chrisspen/saunterbot/circuits/external voltage reference/Vref.png

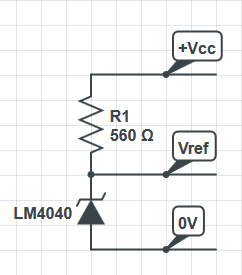
circuits/external voltage reference/Vref.png
