chrisspen/saunterbot/docs/img/bot/IMG_20180331_162108.jpg

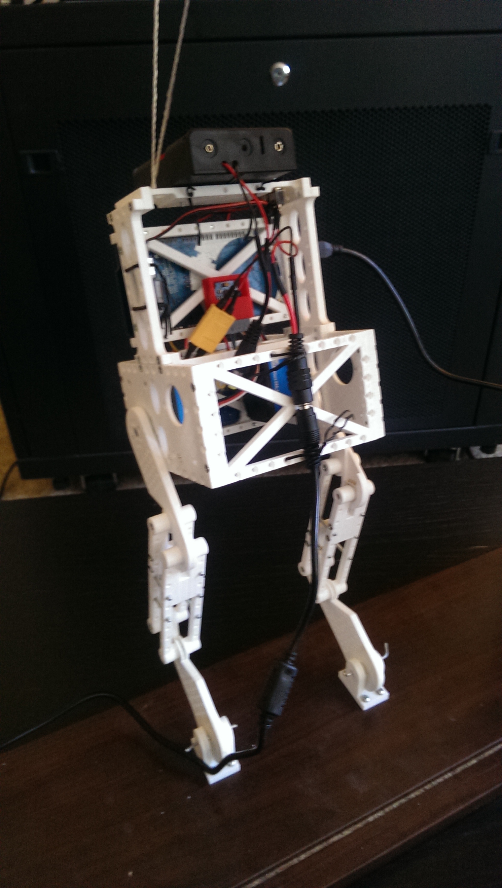
docs/img/bot/IMG_20180331_162108.jpg
