chrisspen/saunterbot/docs/img/bot/IMG_20180331_162210.jpg

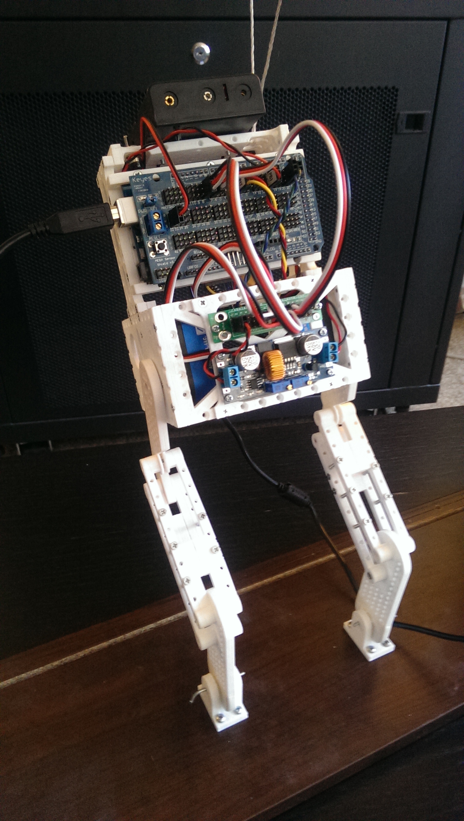
docs/img/bot/IMG_20180331_162210.jpg
