chrisspen/saunterbot/docs/img/bot/IMG_20180411_193514.jpg

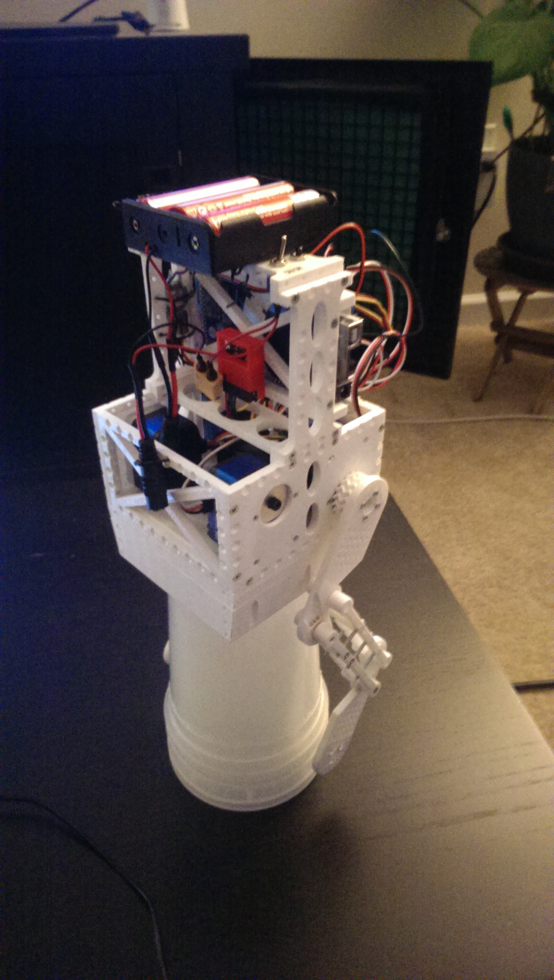
docs/img/bot/IMG_20180411_193514.jpg
