chrisspen/saunterbot/docs/img/bot/IMG_20180411_193522.jpg

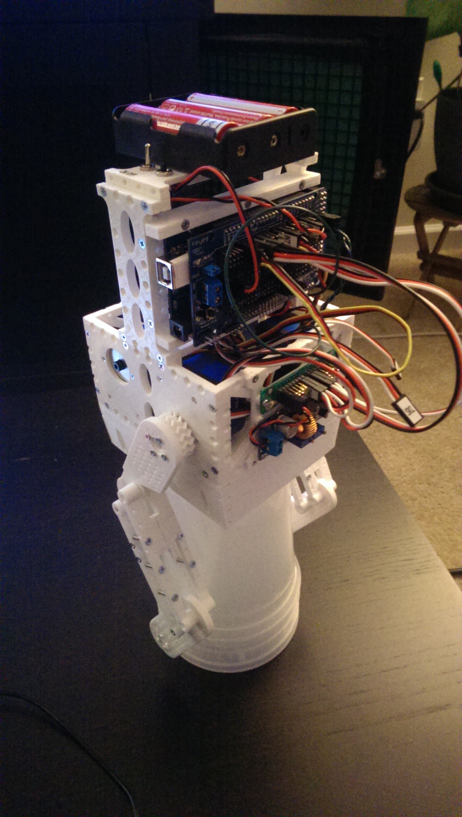
docs/img/bot/IMG_20180411_193522.jpg
