chrisspen/saunterbot/docs/img/bot/IMG_20180411_193531.jpg

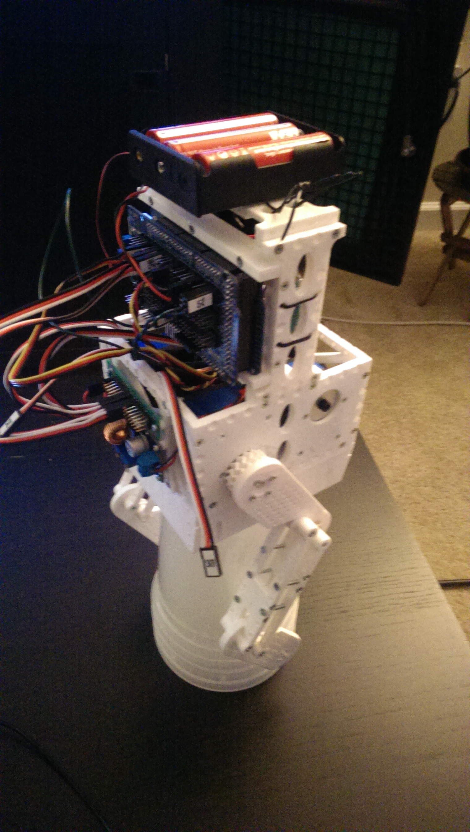
docs/img/bot/IMG_20180411_193531.jpg
