chrisspen/saunterbot/docs/img/bot/IMG_20180411_193601.jpg

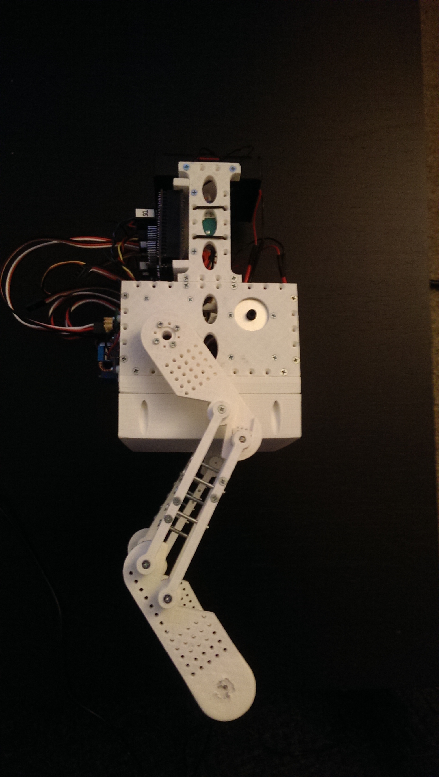
docs/img/bot/IMG_20180411_193601.jpg
