chrisspen/saunterbot/docs/img/bot/IMG_20180411_193617.jpg

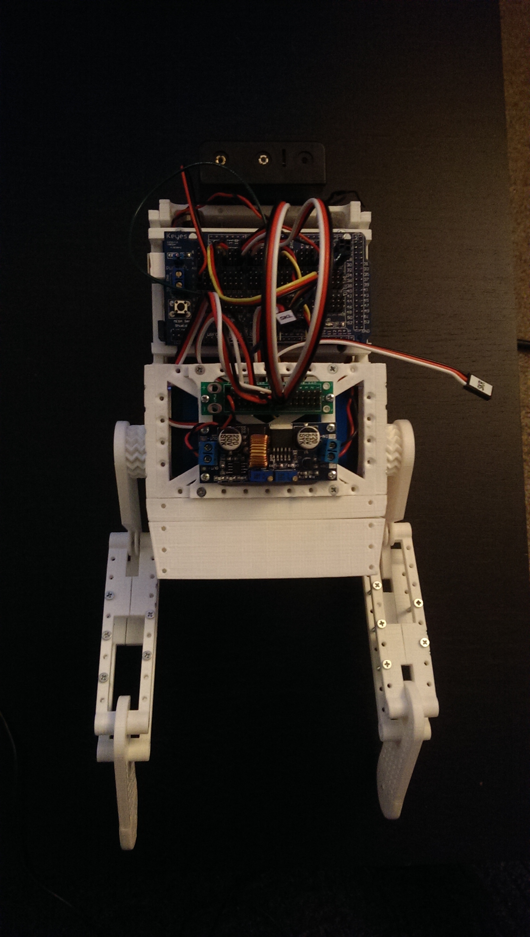
docs/img/bot/IMG_20180411_193617.jpg
