chrisspen/saunterbot/docs/img/bot/layout-cropped.png

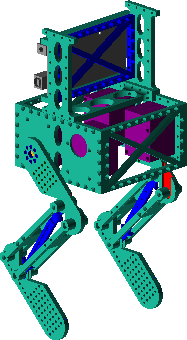
docs/img/bot/layout-cropped.png
