chrisspen/saunterbot/docs/img/bot/layout.png

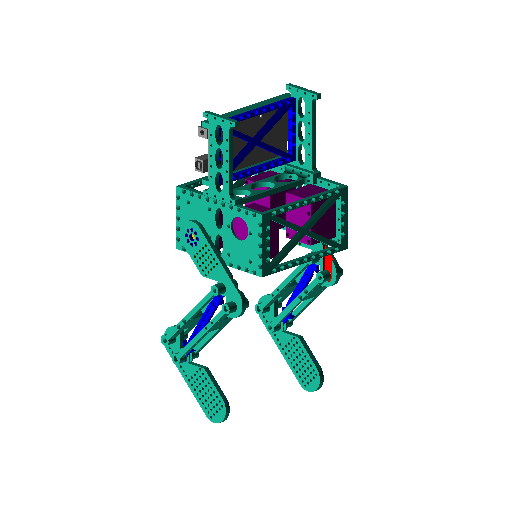
docs/img/bot/layout.png
