chrisspen/saunterbot/docs/img/dynamics-1-20180330.png

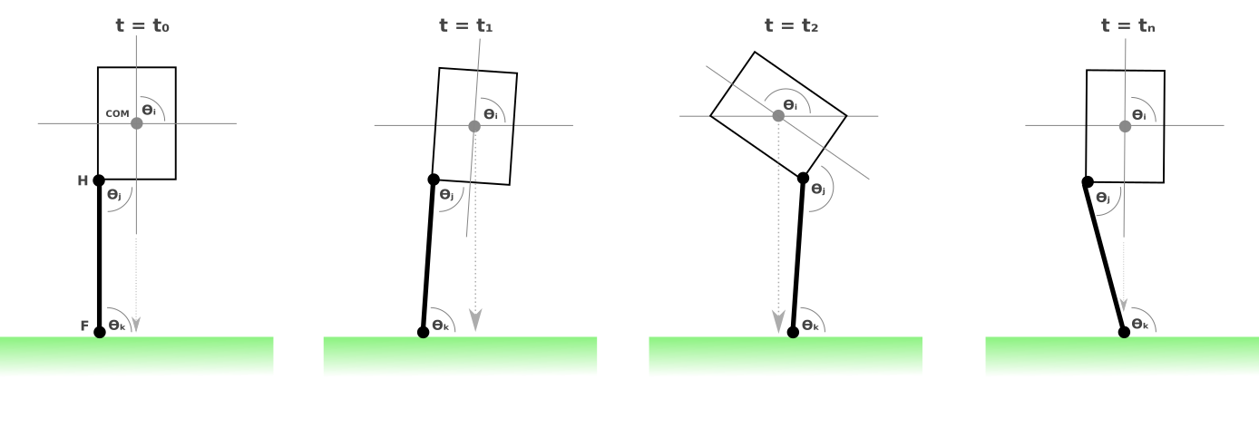
docs/img/dynamics-1-20180330.png
