chrisspen/saunterbot/docs/img/dynamics-1-20180331.png

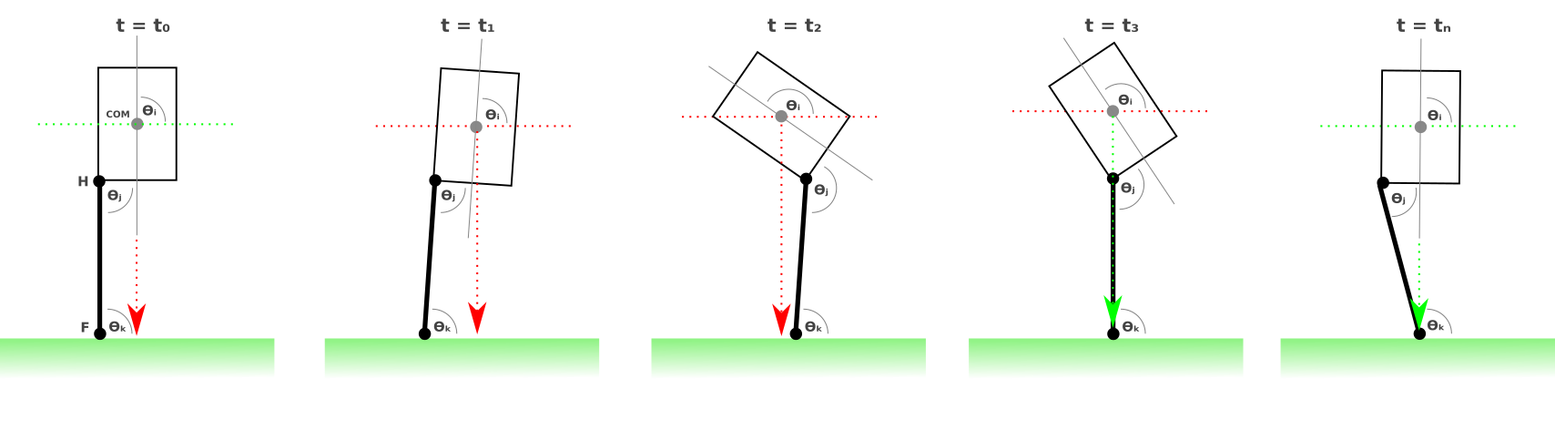
docs/img/dynamics-1-20180331.png
