chrisspen/saunterbot/docs/research/inverted pendulum/An-example-of-cart-table-model9.ppm.png

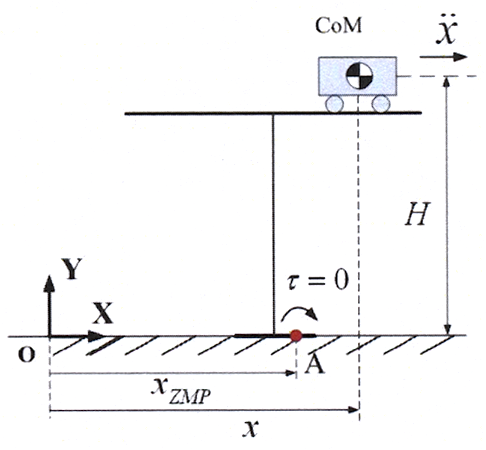
docs/research/inverted pendulum/An-example-of-cart-table-model9.ppm.png
