chrisspen/saunterbot/docs/research/legs/fncom-08-00027-g002.jpg

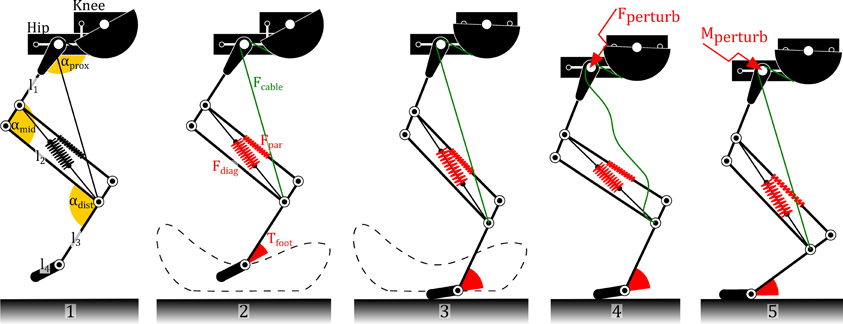
docs/research/legs/fncom-08-00027-g002.jpg
