chrisspen/saunterbot/models/electronics/hs-311-hitec-standard-servo/Renderings/aa.PNG

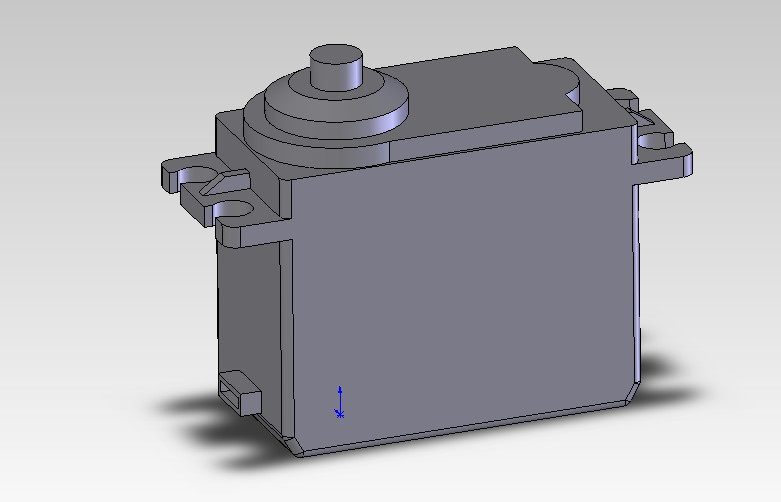
models/electronics/hs-311-hitec-standard-servo/Renderings/aa.PNG
