chrisspen/saunterbot/docs/parts/Arduino - Mega/README

Arduino Mega
============

https://store.arduino.cc/arduino-mega-2560-rev3

https://www.arduino.cc/en/Hacking/PinMapping2560
