chrisspen/saunterbot/docs/parts/Arduino Mega Sensor Shield v2.0/README

Sensor Shield for Arduino MEGA V2

http://yourduino.com/sunshop//index.php?l=product_detail&p=195
https://arduino-info.wikispaces.com/SensorShield
