chrisspen/saunterbot/docs/parts/Rotary Position Sensor - Model 3382/README

Rotary Position Sensor - Model 3382
===================================

https://www.digikey.com/products/en?keywords=3382G-1-104GCT-ND
