chrisspen/saunterbot/docs/parts/Arduino - Nano/README

Arduino Nano
============

https://store.arduino.cc/arduino-nano
