chrisspen/saunterbot/docs/parts/Alturn - Servo - ABRS-5314HTG+HV/futabaconnector.jpg

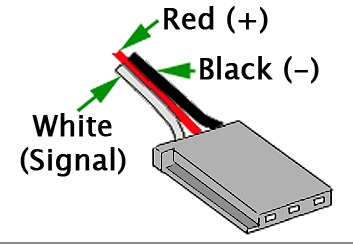
docs/parts/Alturn - Servo - ABRS-5314HTG+HV/futabaconnector.jpg
