chrisspen/saunterbot/docs/parts/Alturn - Servo - ABRS-5314HTG+HV/s-l1600.jpg

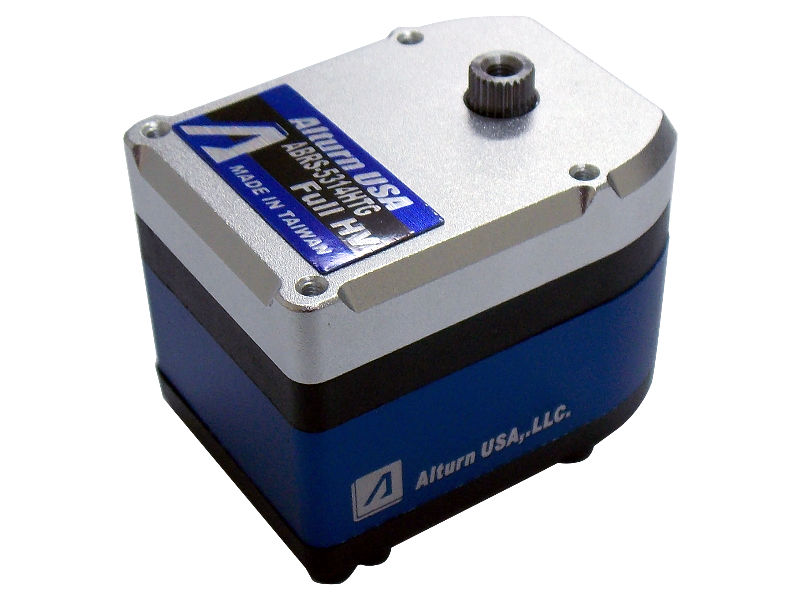
docs/parts/Alturn - Servo - ABRS-5314HTG+HV/s-l1600.jpg
