chrisspen/saunterbot/docs/parts/Arduino Mega Sensor Shield v2.0/large_195_MEGA-SensorShieldV20-1024.jpg

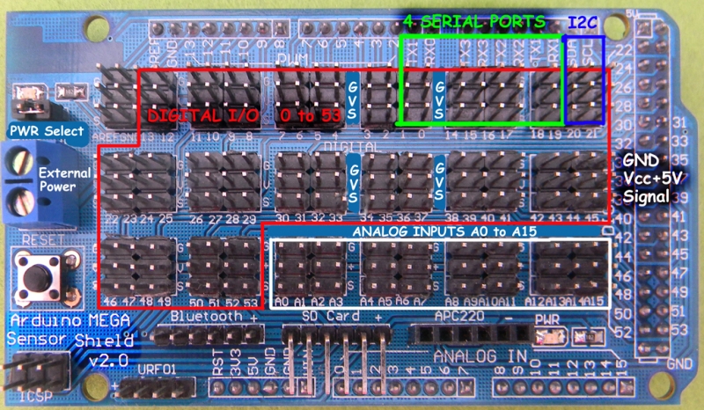
docs/parts/Arduino Mega Sensor Shield v2.0/large_195_MEGA-SensorShieldV20-1024.jpg
