chrisspen/saunterbot/docs/parts/d-sub connectors/220px-DSubminiatures.svg.png

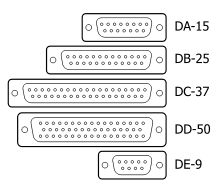
docs/parts/d-sub connectors/220px-DSubminiatures.svg.png
