chrisspen/saunterbot/docs/parts/GY-521 MPU-6050 6-Axis Gryo Accel/61tN3MHdreL._SL1001_.jpg

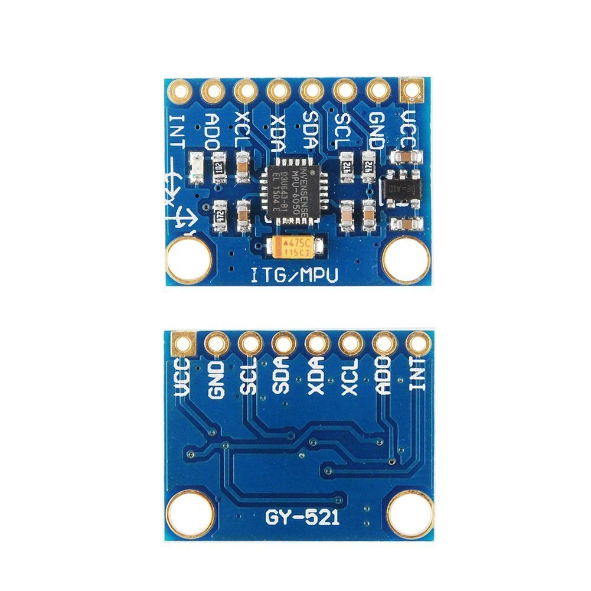
docs/parts/GY-521 MPU-6050 6-Axis Gryo Accel/61tN3MHdreL._SL1001_.jpg
