chrisspen/saunterbot/docs/parts/GY-521 MPU-6050 6-Axis Gryo Accel/71pdoX7o9VL._SL1500_.jpg

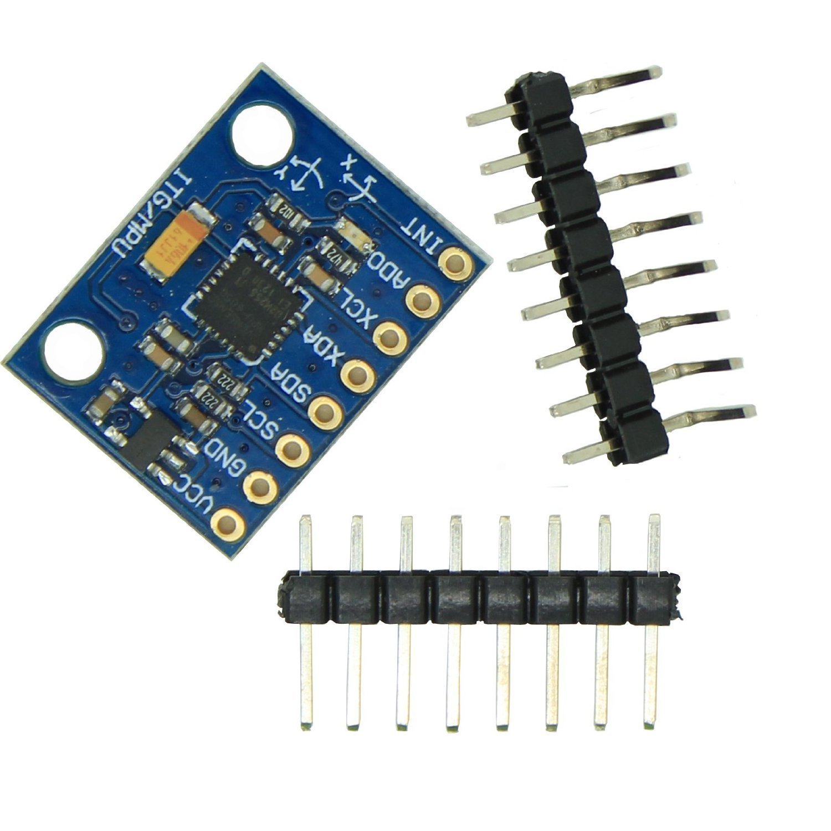
docs/parts/GY-521 MPU-6050 6-Axis Gryo Accel/71pdoX7o9VL._SL1500_.jpg
