chrisspen/saunterbot/docs/parts/Pololu Micro Maestro 6-Channel Servo Controller/0J1949.1200.jpg

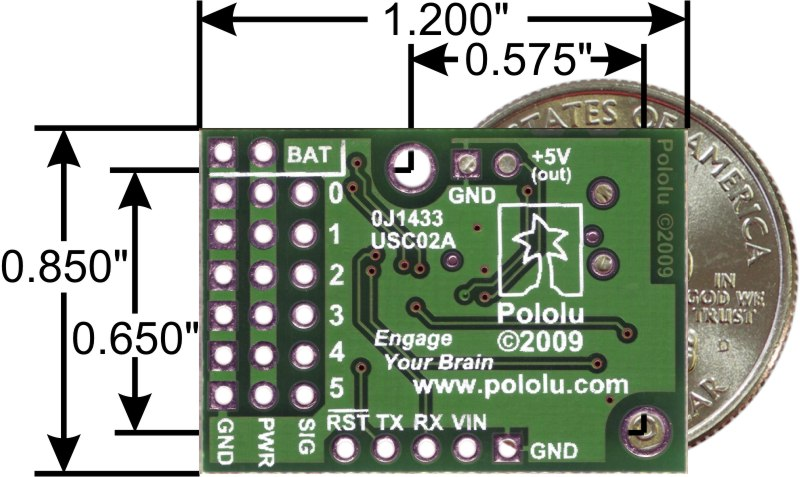
docs/parts/Pololu Micro Maestro 6-Channel Servo Controller/0J1949.1200.jpg
