chrisspen/saunterbot/docs/parts/Thin Film Force Sensor 5kg/51+l82o+N5L._SL1001_.jpg

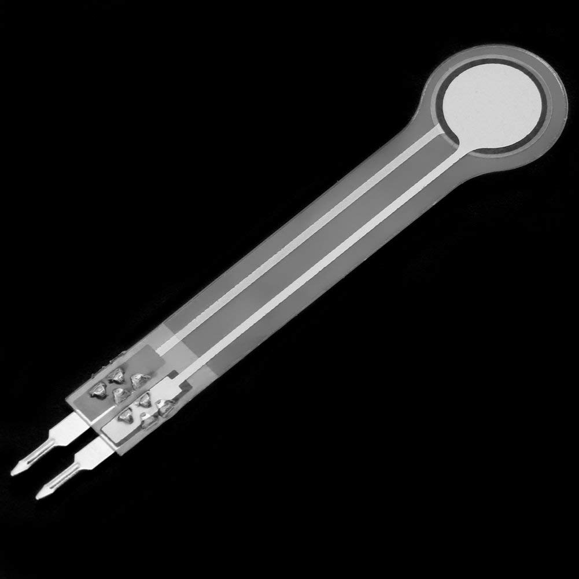
docs/parts/Thin Film Force Sensor 5kg/51+l82o+N5L._SL1001_.jpg
