chrisspen/saunterbot/models/printable/leg_spring.stl

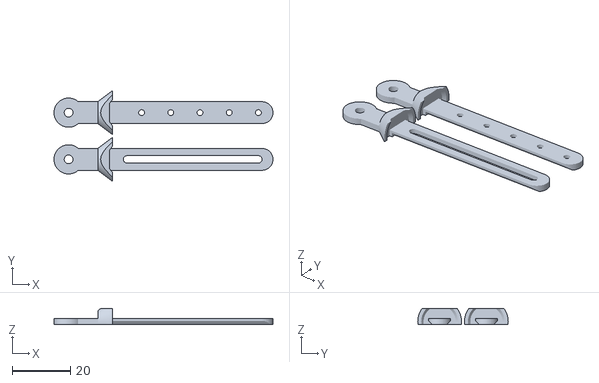
[picture p43: CAD file, 2018-08-15]
models/printable/leg_spring.stl
75.0 x 31.0 x 5.50
