chrisspen/saunterbot/models/printable/leg_hip_axle_round.stl

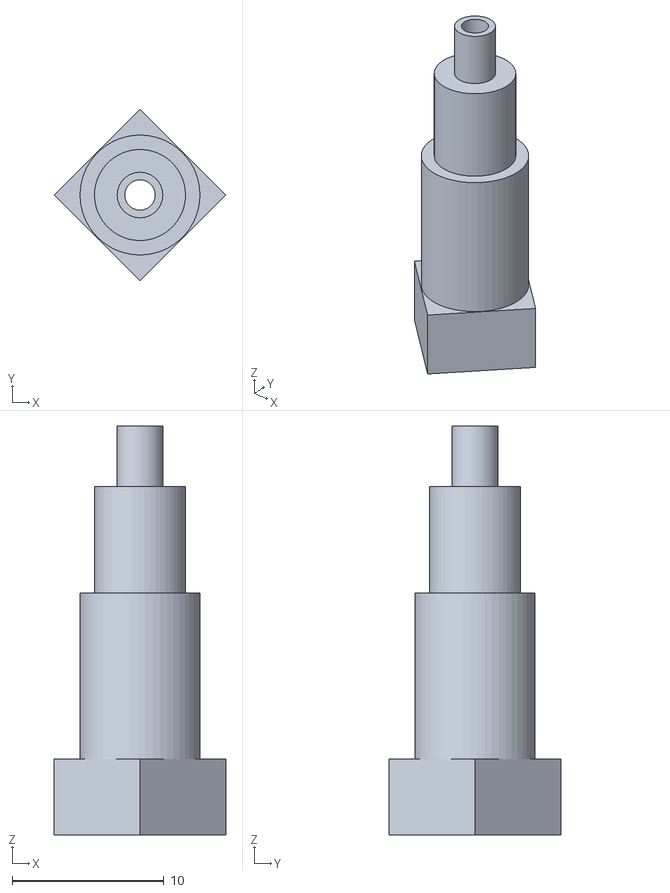
[picture p44: CAD file, 2018-08-15]
models/printable/leg_hip_axle_round.stl
11.3 x 11.3 x 27.0
