chrisspen/saunterbot/models/printable/leg_knee_tendon_anchor_top.stl

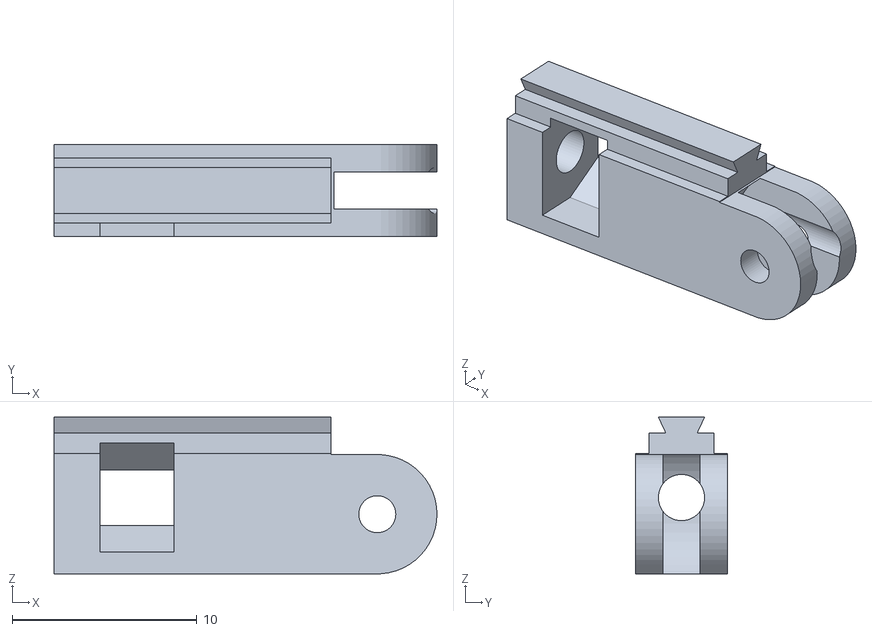
[picture p45: CAD file, 2018-08-15]
models/printable/leg_knee_tendon_anchor_top.stl
20.7 x 5.00 x 8.47
