chrisspen/saunterbot/models/printable/leg_hip_tendon_retainer.stl

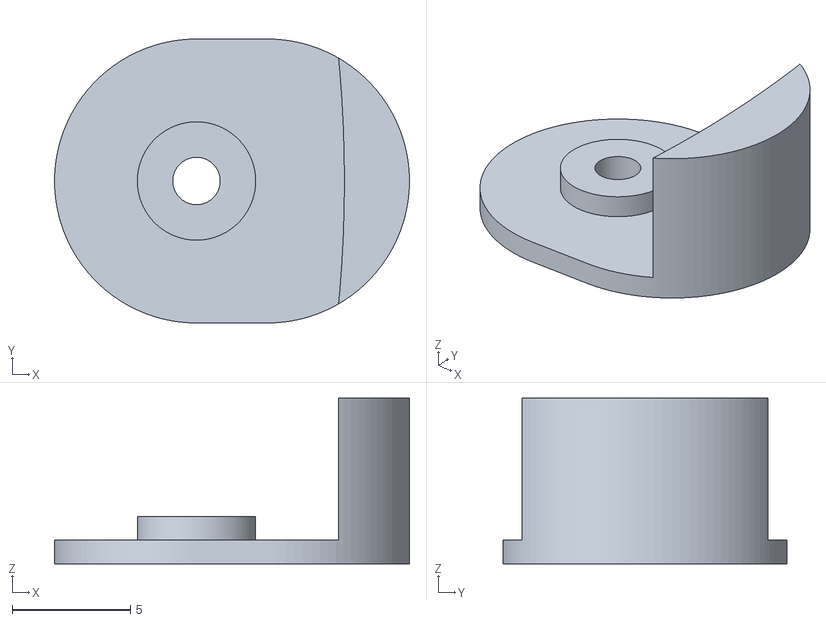
[picture p46: CAD file, 2018-08-15]
models/printable/leg_hip_tendon_retainer.stl
15.0 x 12.0 x 7.00
