chrisspen/saunterbot/models/printable/leg_knee_servo_riser.stl

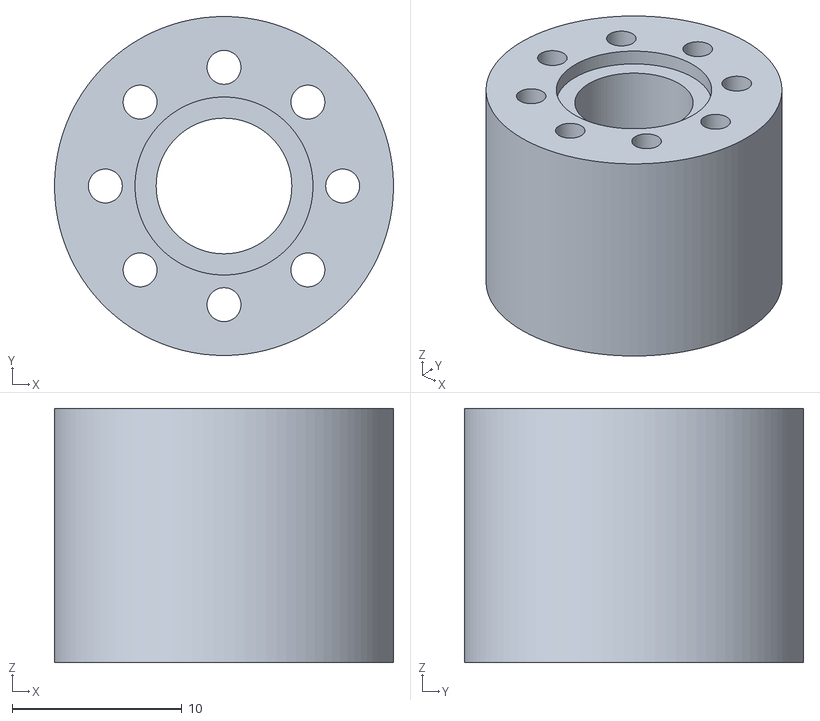
[picture p47: CAD file, 2018-08-15]
models/printable/leg_knee_servo_riser.stl
20.0 x 20.0 x 15.0
