chrisspen/saunterbot/models/printable/leg_spring2.stl

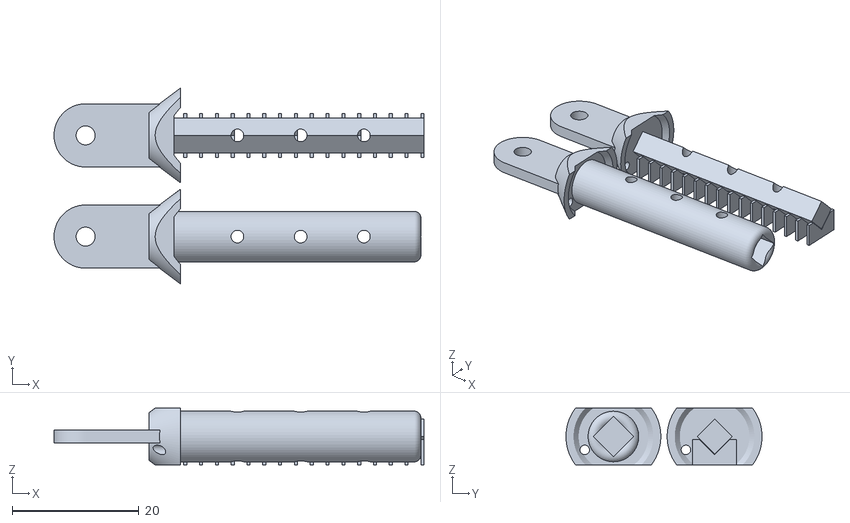
[picture p48: CAD file, 2018-08-15]
models/printable/leg_spring2.stl
58.5 x 31.0 x 9.00
