chrisspen/saunterbot/models/printable/leg_hip_axle.stl

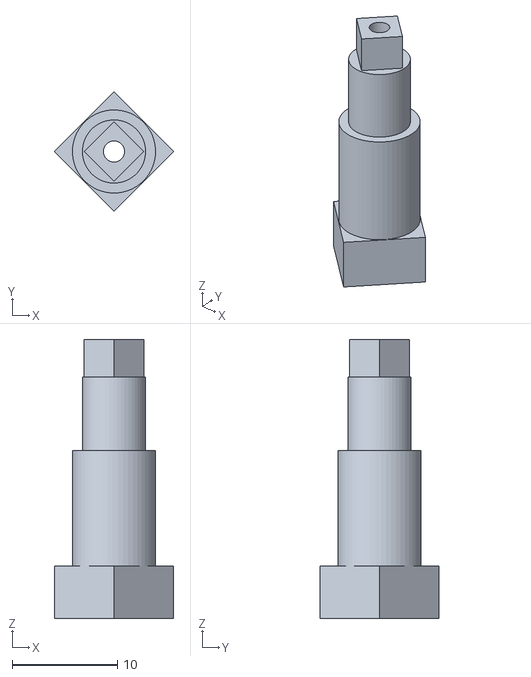
[picture p49: CAD file, 2018-07-29]
models/printable/leg_hip_axle.stl
11.3 x 11.3 x 26.5
