chrisspen/saunterbot/models/printable/leg_hip_holder.stl

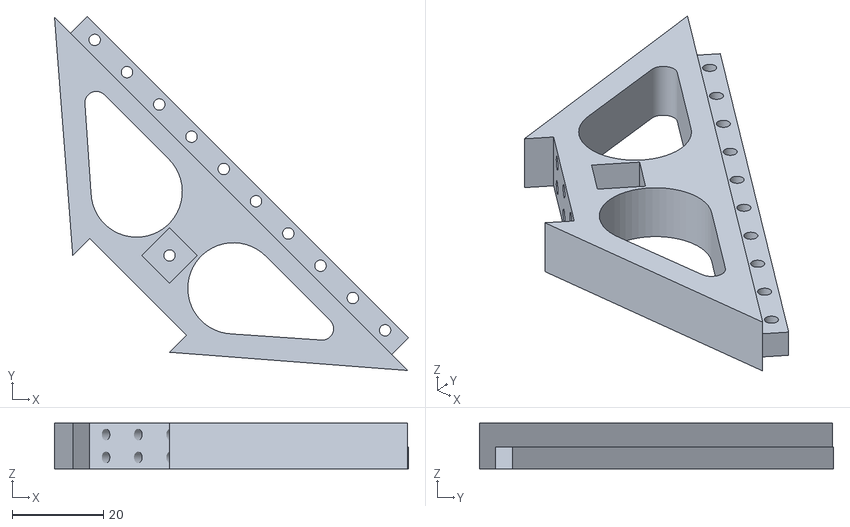
[picture p50: CAD file, 2018-07-29]
models/printable/leg_hip_holder.stl
77.6 x 77.6 x 10.0
