chrisspen/saunterbot/models/printable/balancer_drive_gear.stl

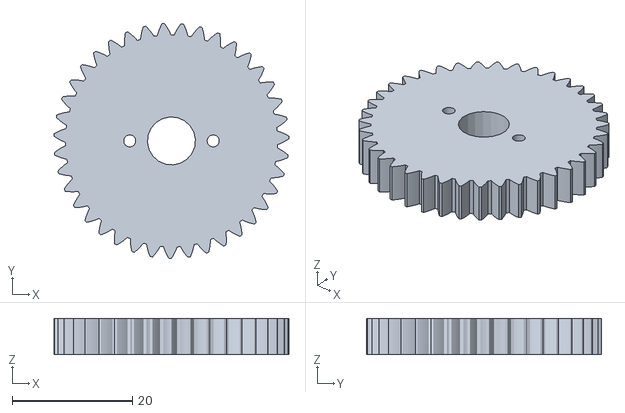
[picture p51: CAD file, 2018-04-12]
models/printable/balancer_drive_gear.stl
39.1 x 39.1 x 6.00
