chrisspen/saunterbot/models/printable/balancer_gear_axle_top.stl

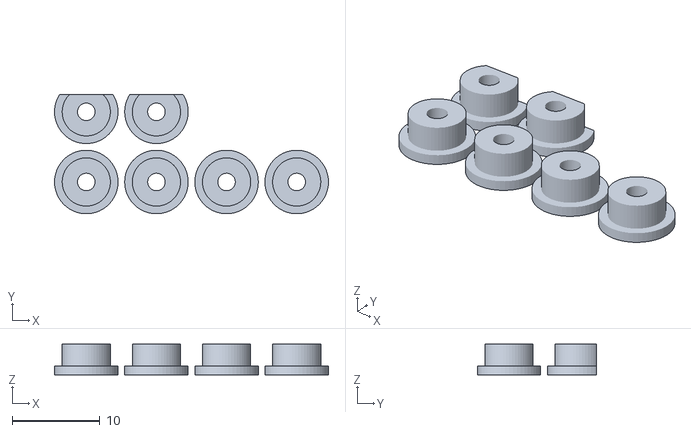
[picture p52: CAD file, 2018-04-12]
models/printable/balancer_gear_axle_top.stl
31.2 x 13.6 x 3.50
