chrisspen/saunterbot/models/printable/balancer_opposite_gear.stl

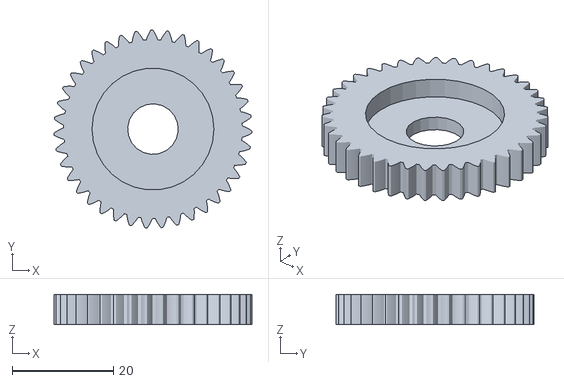
[picture p53: CAD file, 2018-04-12]
models/printable/balancer_opposite_gear.stl
39.1 x 39.1 x 6.00
