chrisspen/saunterbot/models/printable/balancer_top_plate.stl

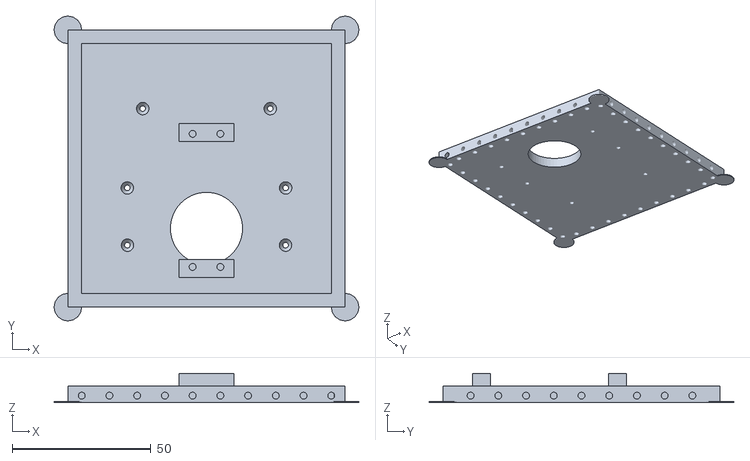
[picture p54: CAD file, 2018-04-12]
models/printable/balancer_top_plate.stl
110.0 x 110.0 x 10.5
