chrisspen/saunterbot/models/printable/balancer_weight_container.stl

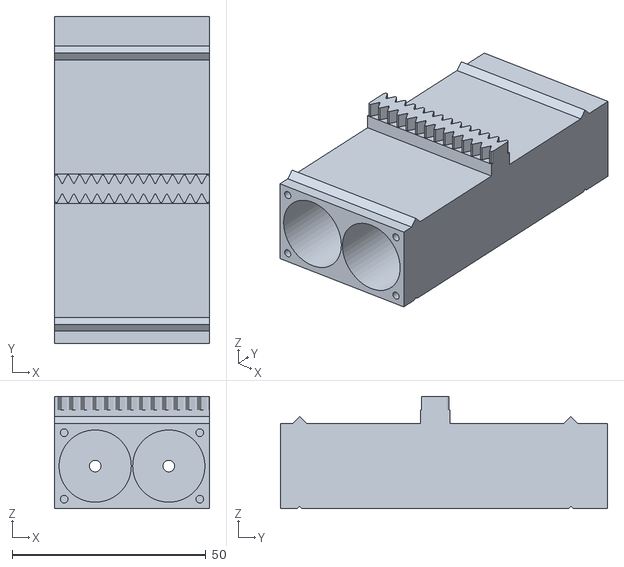
[picture p55: CAD file, 2018-04-12]
models/printable/balancer_weight_container.stl
40.0 x 84.5 x 29.0
