chrisspen/saunterbot/models/printable/balancer_bottom_plate.stl

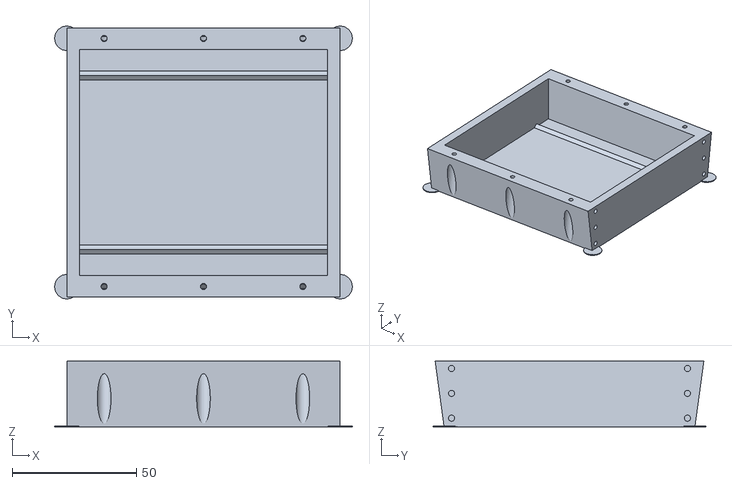
[picture p56: CAD file, 2018-04-12]
models/printable/balancer_bottom_plate.stl
120.0 x 110.0 x 26.5
