chrisspen/saunterbot/models/printable/leg_hip_spacer.stl

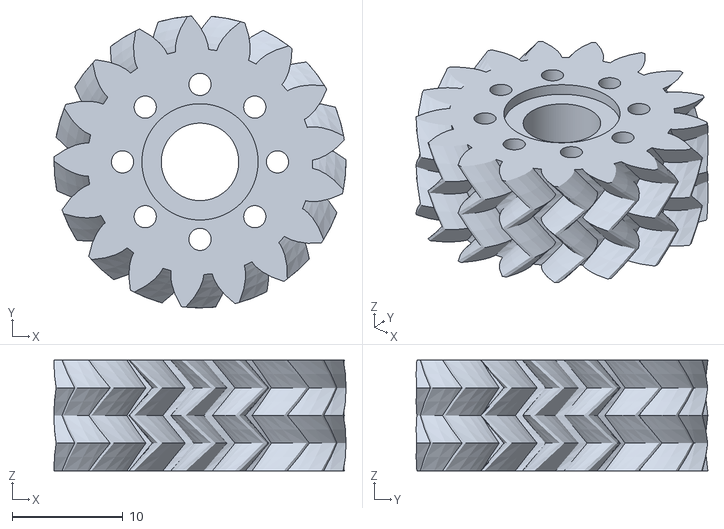
[picture p57: CAD file, 2018-04-12]
models/printable/leg_hip_spacer.stl
26.4 x 26.4 x 10.0
