chrisspen/saunterbot/models/printable/balancer_translation_gear.stl

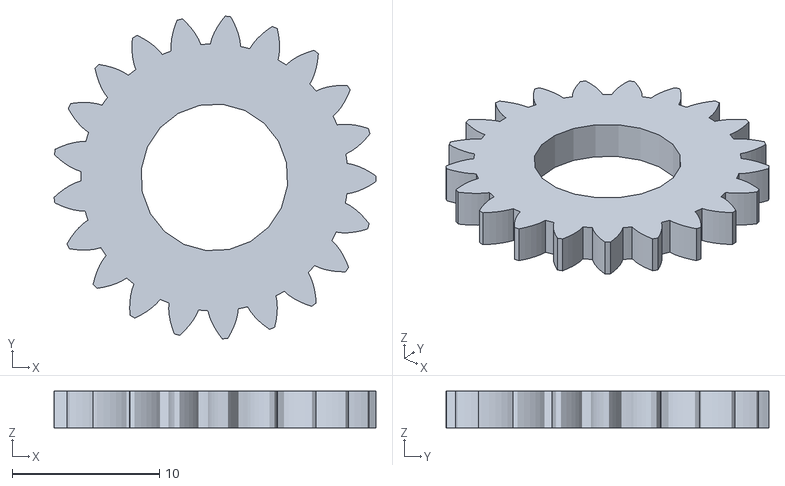
[picture p58: CAD file, 2018-04-12]
models/printable/balancer_translation_gear.stl
21.9 x 21.9 x 2.50
