chrisspen/saunterbot/models/printable/balancer_middle_plate.stl

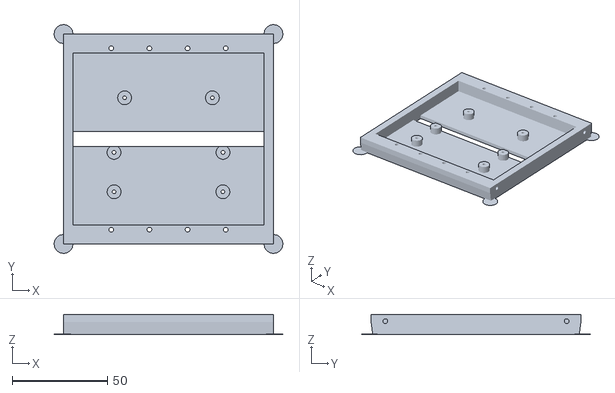
[picture p59: CAD file, 2018-04-12]
models/printable/balancer_middle_plate.stl
120.0 x 120.0 x 10.5
