chrisspen/saunterbot/models/printable/balancer_weight_container_door.stl

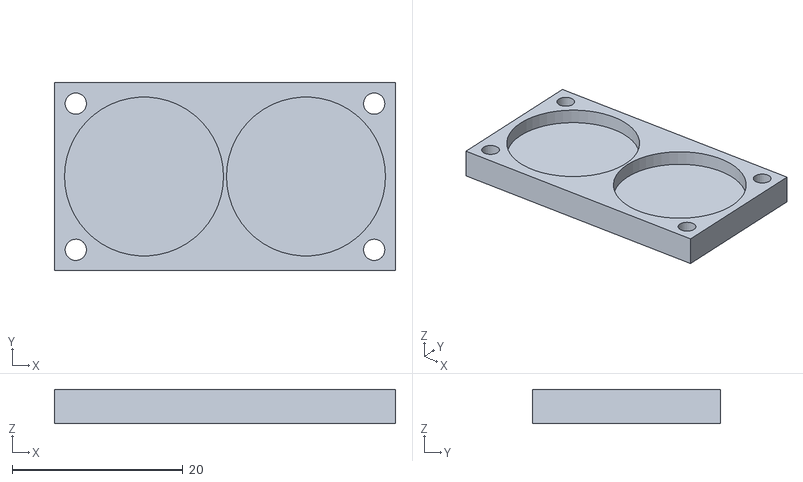
[picture p60: CAD file, 2018-04-12]
models/printable/balancer_weight_container_door.stl
40.0 x 22.0 x 4.00
