chrisspen/saunterbot/models/printable/motors_alturn_abrs_5314htg_hv.stl

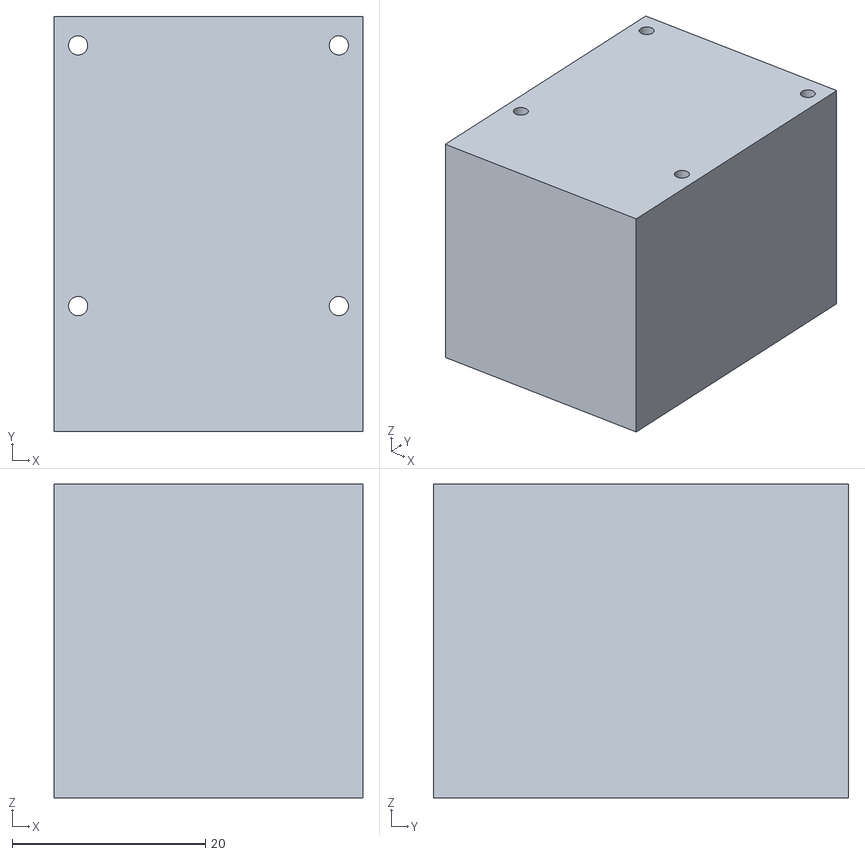
[picture p61: CAD file, 2018-03-31]
models/printable/motors_alturn_abrs_5314htg_hv.stl
32.0 x 43.0 x 32.5
