chrisspen/saunterbot/models/printable/foot_pivot.stl

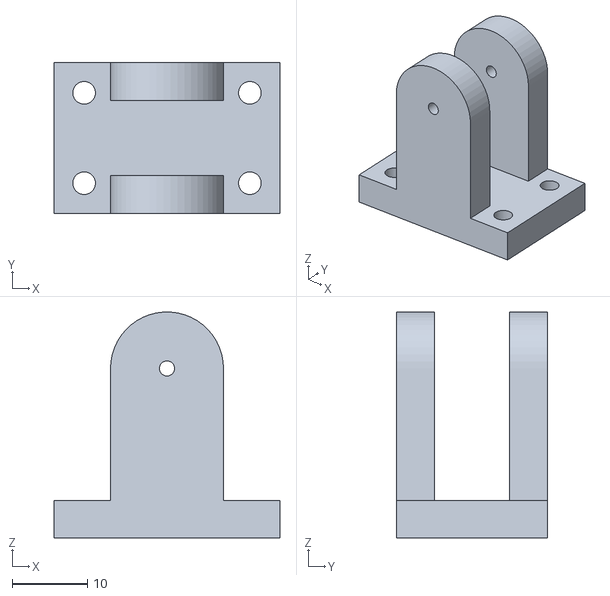
[picture p62: CAD file, 2018-03-31]
models/printable/foot_pivot.stl
30.0 x 20.0 x 30.0
