chrisspen/saunterbot/models/printable/dc_converter_tray.stl

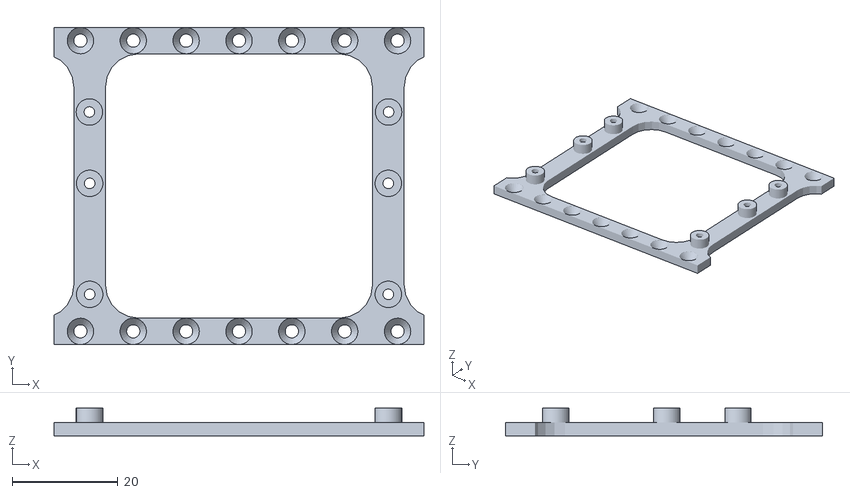
[picture p63: CAD file, 2018-03-31]
models/printable/dc_converter_tray.stl
70.0 x 60.0 x 5.25
