chrisspen/saunterbot/models/printable/arduino_mega_mount_top.stl

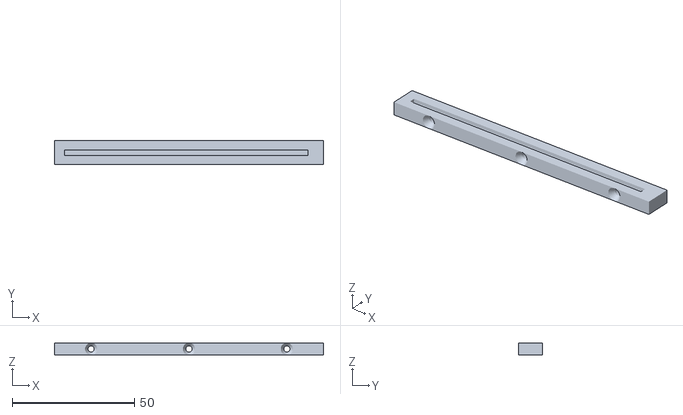
[picture p64: CAD file, 2018-03-27]
models/printable/arduino_mega_mount_top.stl
110.0 x 10.0 x 5.00
