chrisspen/saunterbot/models/printable/leg_middle.stl

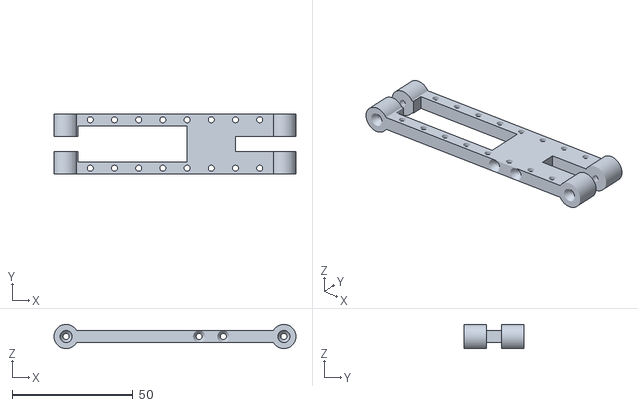
[picture p65: CAD file, 2018-03-27]
models/printable/leg_middle.stl
100.0 x 25.0 x 9.98
