chrisspen/saunterbot/models/printable/battery_holder_strut.stl

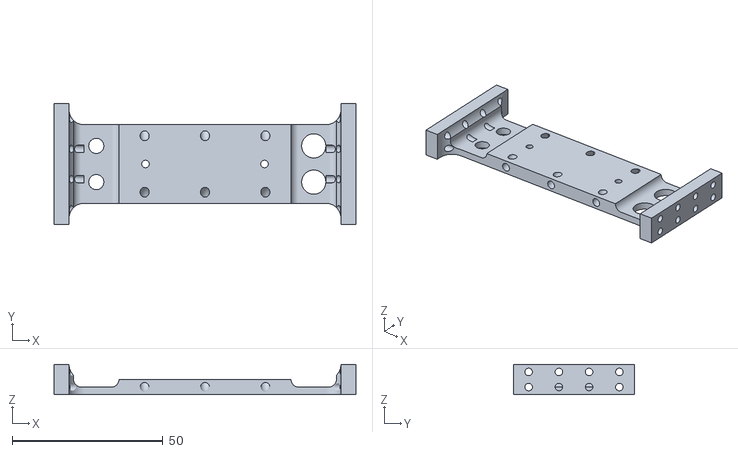
[picture p66: CAD file, 2018-03-27]
models/printable/battery_holder_strut.stl
100.0 x 40.0 x 10.0
