chrisspen/saunterbot/models/printable/leg_upper.stl

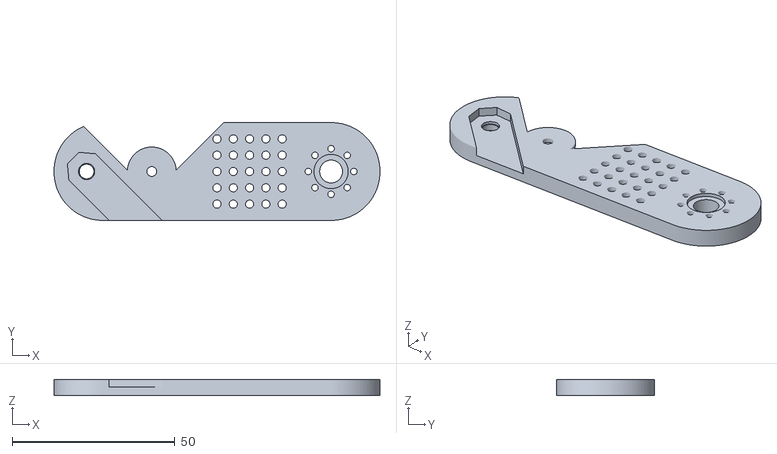
[picture p67: CAD file, 2018-03-27]
models/printable/leg_upper.stl
100.0 x 30.0 x 5.00
