chrisspen/saunterbot/models/printable/arduino_mega_mount.stl

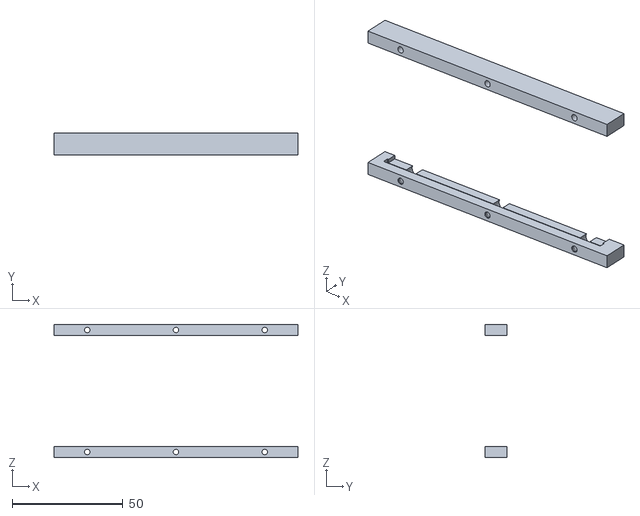
[picture p68: CAD file, 2018-03-27]
models/printable/arduino_mega_mount.stl
110.0 x 10.0 x 60.0
