chrisspen/saunterbot/models/printable/leg_middle_top_a.stl

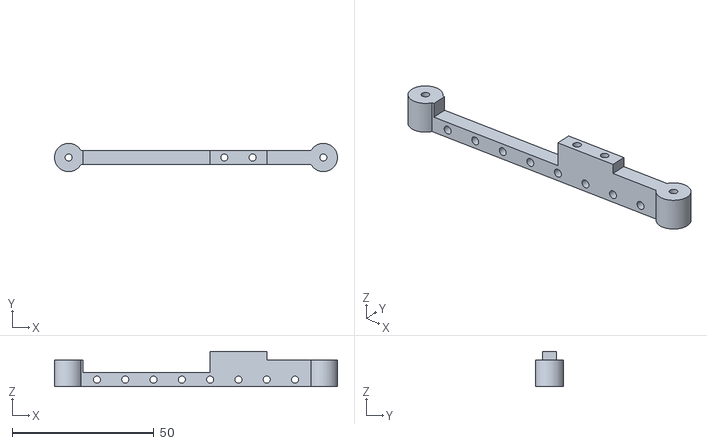
[picture p69: CAD file, 2018-03-27]
models/printable/leg_middle_top_a.stl
100.0 x 9.98 x 12.5
