chrisspen/saunterbot/models/printable/pelvis_motor_face_mirrored.stl

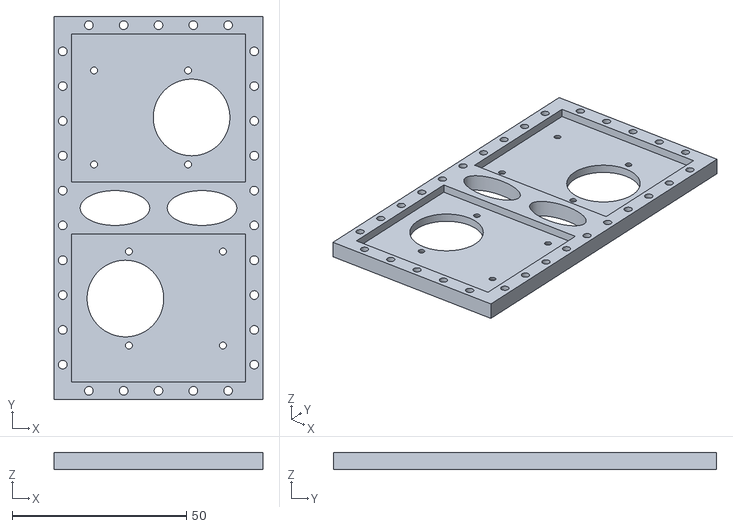
[picture p70: CAD file, 2018-03-27]
models/printable/pelvis_motor_face_mirrored.stl
60.0 x 110.0 x 5.00
