chrisspen/saunterbot/models/printable/pelvis_torso_strut.stl

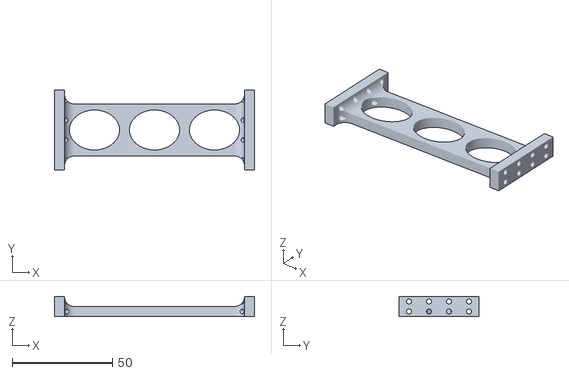
[picture p71: CAD file, 2018-03-27]
models/printable/pelvis_torso_strut.stl
100.0 x 40.0 x 10.0
