chrisspen/saunterbot/models/printable/leg_middle_top_b.stl

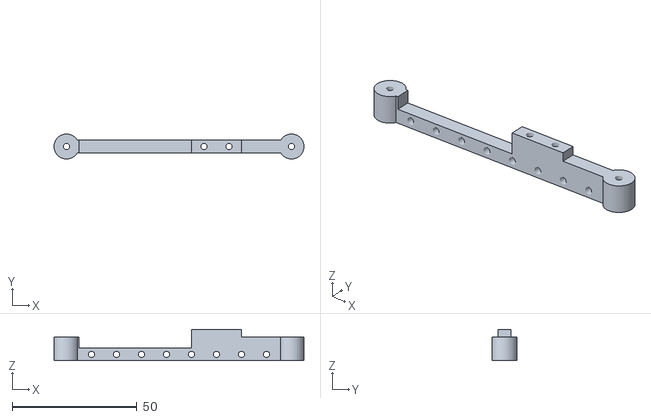
[picture p72: CAD file, 2018-03-27]
models/printable/leg_middle_top_b.stl
100.0 x 9.98 x 12.5
