chrisspen/saunterbot/models/printable/leg_middle_bottom_b.stl

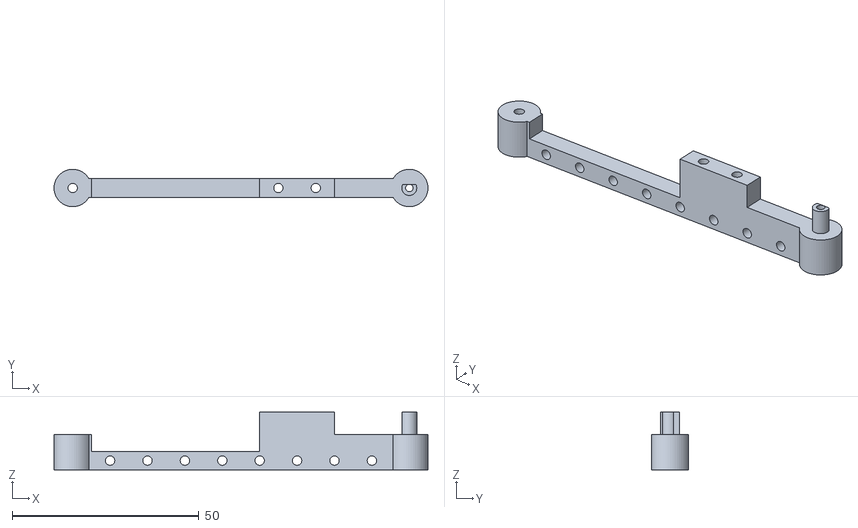
[picture p73: CAD file, 2018-03-27]
models/printable/leg_middle_bottom_b.stl
100.0 x 9.98 x 15.5
