chrisspen/saunterbot/models/printable/leg_lower.stl

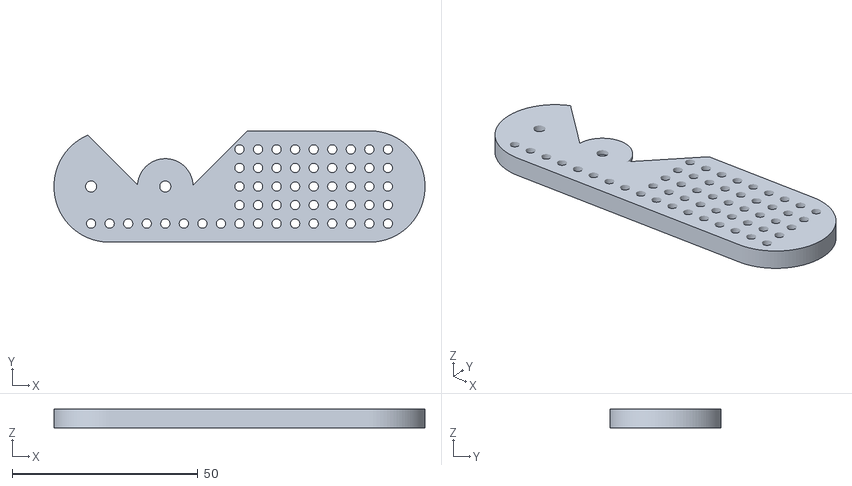
[picture p74: CAD file, 2018-03-27]
models/printable/leg_lower.stl
100.0 x 30.0 x 5.00
