chrisspen/saunterbot/models/printable/leg_middle_bottom_a.stl

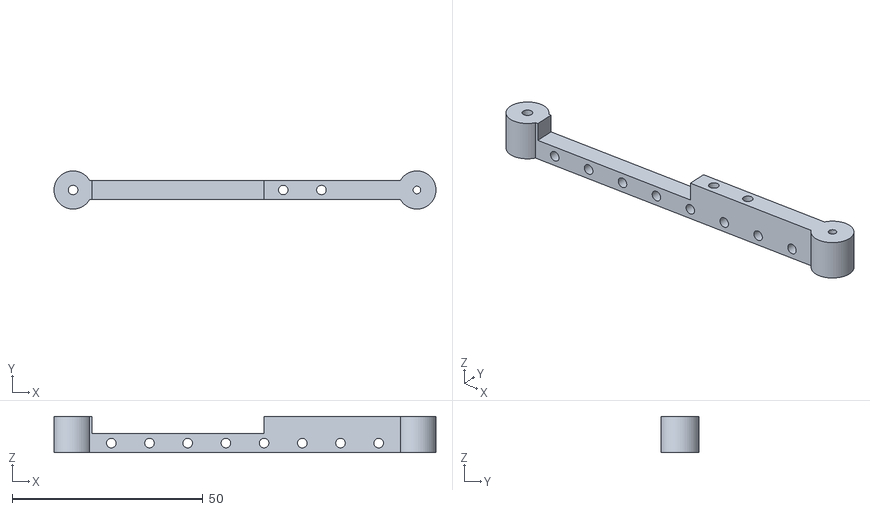
[picture p75: CAD file, 2018-03-27]
models/printable/leg_middle_bottom_a.stl
100.0 x 9.98 x 9.50
