chrisspen/saunterbot/models/printable/pelvis_cross_support.stl

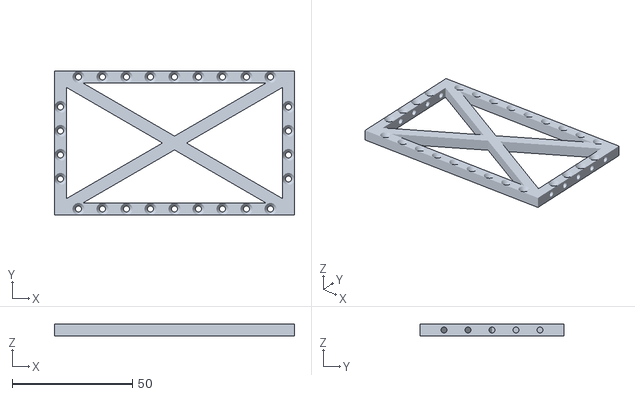
[picture p76: CAD file, 2018-03-27]
models/printable/pelvis_cross_support.stl
100.0 x 60.0 x 5.00
