chrisspen/saunterbot/models/printable/torso_side.stl

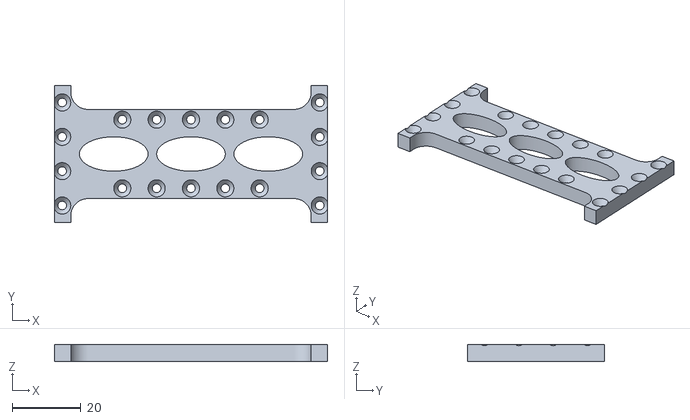
[picture p77: CAD file, 2018-03-27]
models/printable/torso_side.stl
79.5 x 40.0 x 5.00
