chrisspen/saunterbot/models/balancer_drive_gear.scad

use <balancer.scad>;

balancer_drive_gear();
