chrisspen/saunterbot/models/leg_hip_axle.scad

use <leg_hip_holder.scad>;


if(1)
rotate([0,0,45])
rotate([0,90,0])
leg_hip_axle();
