chrisspen/saunterbot/models/leg_hip_brace.scad

module leg_hip_brace(){
}

leg_hip_brace();
