chrisspen/saunterbot/models/leg_hip_cap.scad

module leg_hip_cap(){
}

leg_hip_cap();
