chrisspen/saunterbot/models/leg_knee_tendon_anchor_bottom.scad

use <leg_knee_tendon_anchor.scad>;


leg_knee_tendon_anchor_bottom();
