chrisspen/saunterbot/models/leg_knee_tendon_anchor_bottom_mirrored.scad

use <leg_knee_tendon_anchor.scad>;

mirror([0,1,0])
leg_knee_tendon_anchor_bottom();
