chrisspen/saunterbot/models/leg_knee_tendon_anchor_top.scad

use <leg_knee_tendon_anchor.scad>;

rotate([180,0,0])
leg_knee_tendon_anchor_top();
