chrisspen/saunterbot/models/leg_middle_top_a.scad

use <leg_middle.scad>;

rotate([90,0,0])
leg_middle_top_a();
