chrisspen/saunterbot/models/leg_spring2_female.scad

use <leg_spring2.scad>;

rotate([0,0,90])
make_leg_spring_upper(track=1);
