chrisspen/saunterbot/models/leg_spring_hinge_extender_mirrored.scad

use <leg_spring_hinge_extender.scad>;

mirror([0,1,0])
rotate([-90,0,0])
leg_spring_hinge_extender();
