chrisspen/saunterbot/models/leg_upper_mirrored.scad

use <leg_upper.scad>;

rotate([180,0,0])
mirror([0,0,1])
leg_upper();
