chrisspen/saunterbot/models/pelvis_motor_face.scad

use <pelvis.scad>;

rotate([0,90,0])
pelvis_motor_face();
