chrisspen/saunterbot/models/pelvis_motor_face_mirrored.scad

use <pelvis.scad>;

mirror([1,0,0])
rotate([0,90,0])
pelvis_motor_face();
