chrisspen/saunterbot/models/balancer_gear_washer.scad

difference(){
    cylinder(d=17, h=.4*3, center=true, $fn=50);
    cylinder(d=8, h=2*2, center=true, $fn=50);
}
