chrisspen/saunterbot/models/balancer_middle_plate.scad

use <balancer.scad>;

balancer_middle_plate();

for(j=[-1:2:1])
for(i=[-1:2:1])
translate([55*i,55*j,0.4/2-5/2-10.5])
cylinder(d=10, h=0.4, center=true);
