chrisspen/saunterbot/models/balancer_opposite_gear.scad

use <balancer.scad>;

rotate([180,0,0])
balancer_opp_gear();
