chrisspen/saunterbot/models/balancer_translation_gear.scad

use <balancer.scad>;

balancer_translation_gear();
