chrisspen/saunterbot/models/balancer_weight_container.scad

use <balancer.scad>;

balancer_weight_container();
