chrisspen/saunterbot/models/balancer_weight_container_door.scad

use <balancer.scad>;

rotate([90,0,0])
balancer_weight_container_door();
