chrisspen/saunterbot/models/battery_holder_strut.scad

use <pelvis_torso_strut.scad>;

battery_torso_strut();
