chrisspen/saunterbot/models/pelvis_cross_support.scad

use <pelvis.scad>;

rotate([90,0,0])
pelvis_cross_support();
