chrisspen/saunterbot/docs/parts/ServoCity - Servo Power Board/SC7135-Assembled-Servo-Power-Board-End-600px-with-text.jpg

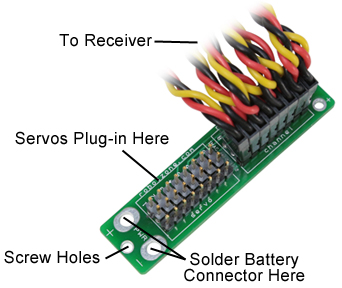
docs/parts/ServoCity - Servo Power Board/SC7135-Assembled-Servo-Power-Board-End-600px-with-text.jpg
