chrisspen/saunterbot/docs/parts/ServoCity - Servo Power Board/SC7135-Unassembled-Servo-Power-Board-600px-with-text.jpg

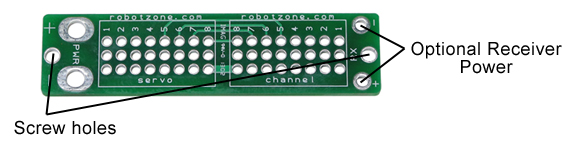
docs/parts/ServoCity - Servo Power Board/SC7135-Unassembled-Servo-Power-Board-600px-with-text.jpg
