chrisspen/saunterbot/docs/parts/ServoCity - Servo Power Board/sc71350_unassembled_power_board_1500px.jpg

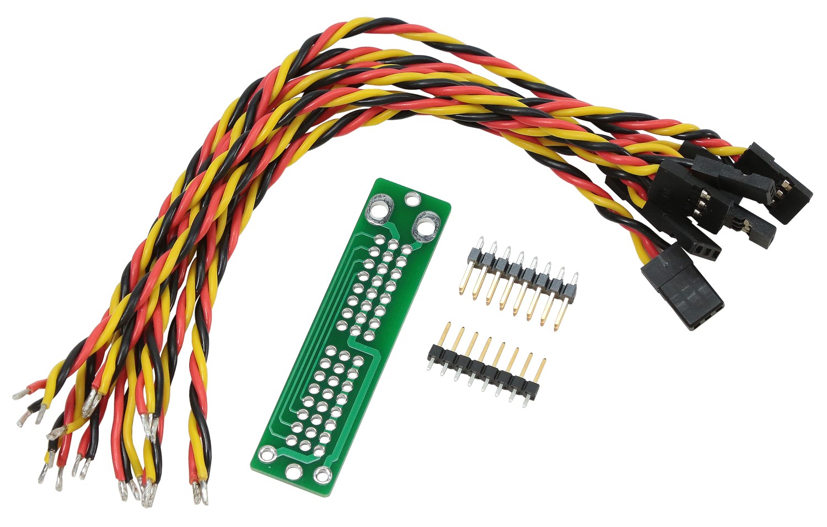
docs/parts/ServoCity - Servo Power Board/sc71350_unassembled_power_board_1500px.jpg
