chrisspen/saunterbot/models/printable/arduino_mega_mount.png

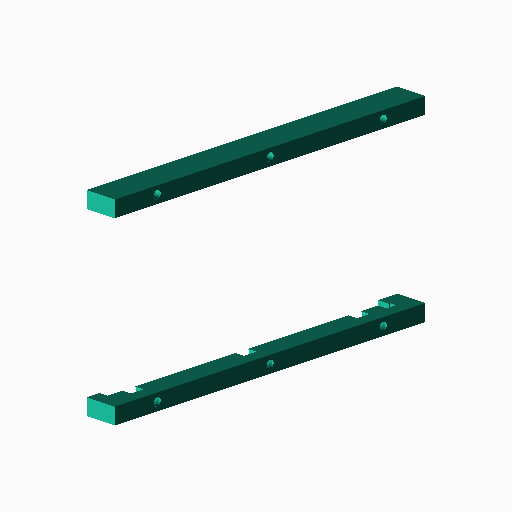
models/printable/arduino_mega_mount.png
