chrisspen/saunterbot/models/printable/arduino_mega_mount_bottom.png

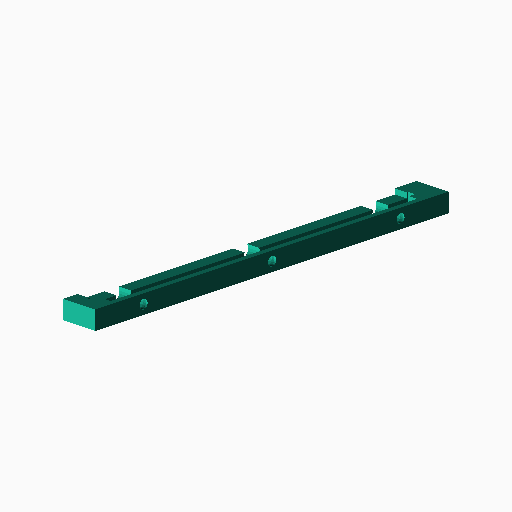
models/printable/arduino_mega_mount_bottom.png
