chrisspen/saunterbot/models/printable/balancer_bottom_plate.png

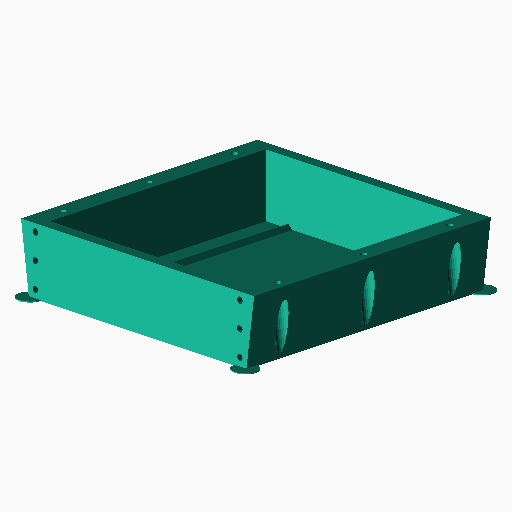
models/printable/balancer_bottom_plate.png
