chrisspen/saunterbot/models/printable/balancer_drive_gear.png

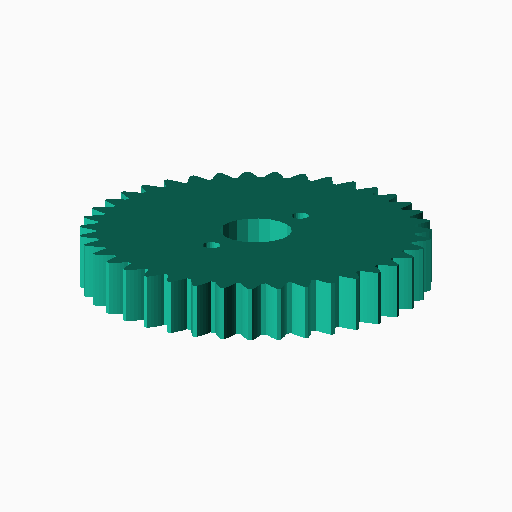
models/printable/balancer_drive_gear.png
