chrisspen/saunterbot/models/printable/balancer_gear_axle_top.png

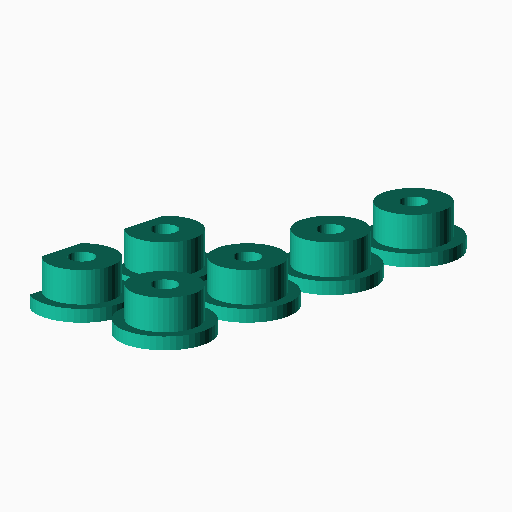
models/printable/balancer_gear_axle_top.png
