chrisspen/saunterbot/models/printable/balancer_gear_washer.png

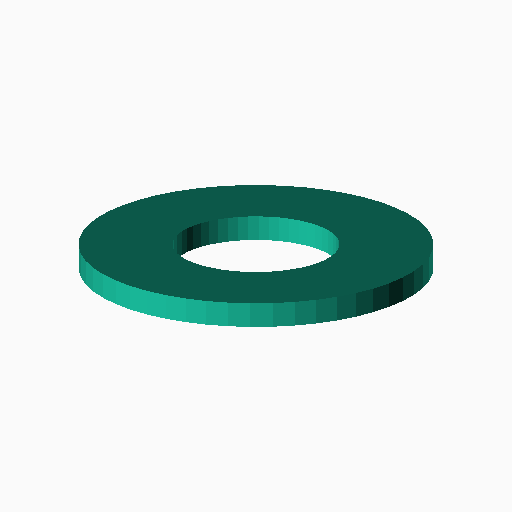
models/printable/balancer_gear_washer.png
