chrisspen/saunterbot/models/printable/balancer_middle_plate.png

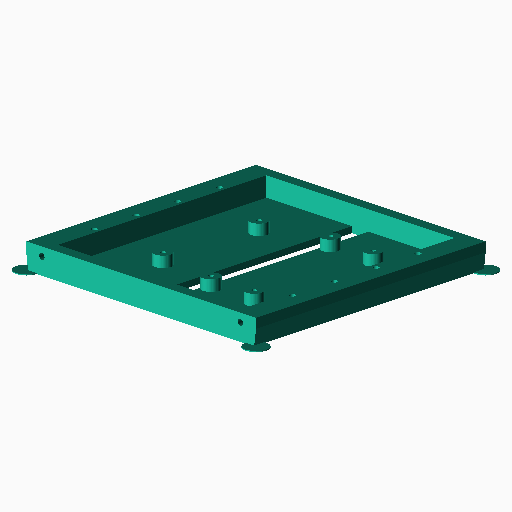
models/printable/balancer_middle_plate.png
