chrisspen/saunterbot/models/printable/balancer_weight_container.png

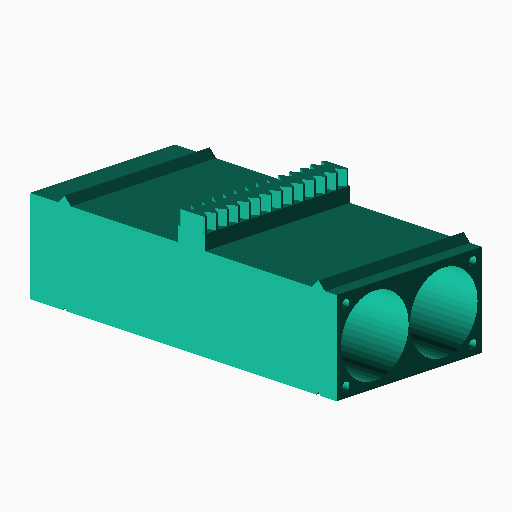
models/printable/balancer_weight_container.png
