chrisspen/saunterbot/models/printable/balancer_weight_container_door.png

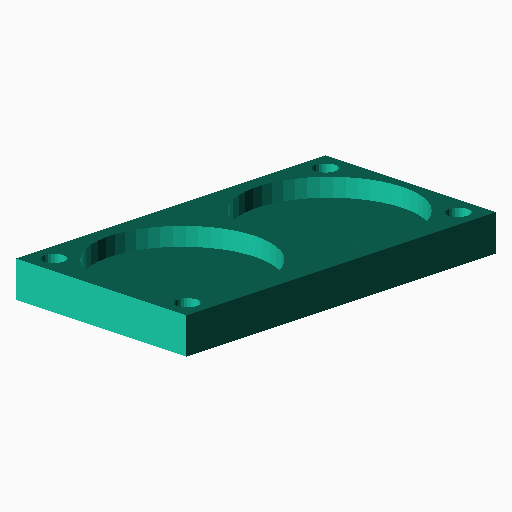
models/printable/balancer_weight_container_door.png
