chrisspen/saunterbot/models/printable/battery_holder_strut.png

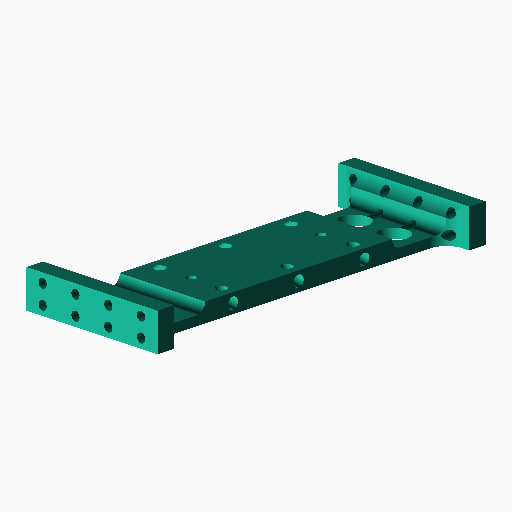
models/printable/battery_holder_strut.png
