chrisspen/saunterbot/models/printable/foot_mock.png

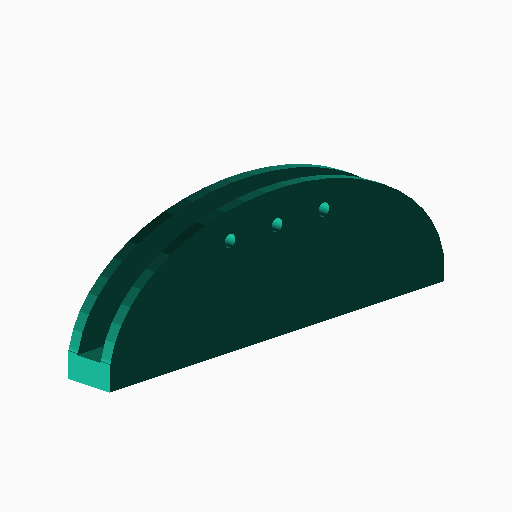
models/printable/foot_mock.png
