chrisspen/saunterbot/models/printable/foot_mock_ankle.png

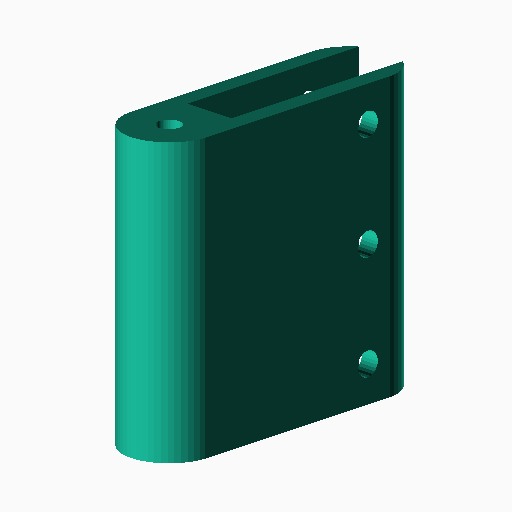
models/printable/foot_mock_ankle.png
