chrisspen/saunterbot/models/printable/foot_mock_core.png

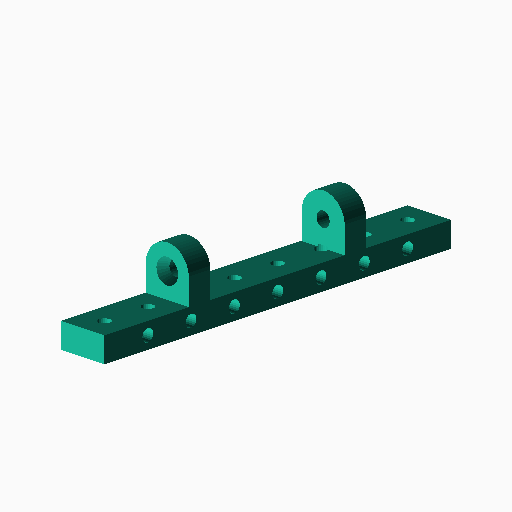
models/printable/foot_mock_core.png
