chrisspen/saunterbot/models/printable/foot_mock_toe.png

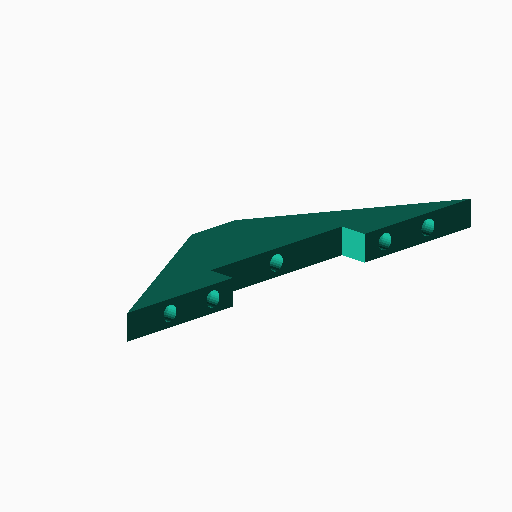
models/printable/foot_mock_toe.png
