chrisspen/saunterbot/models/printable/foot_mock_toe_spring.png

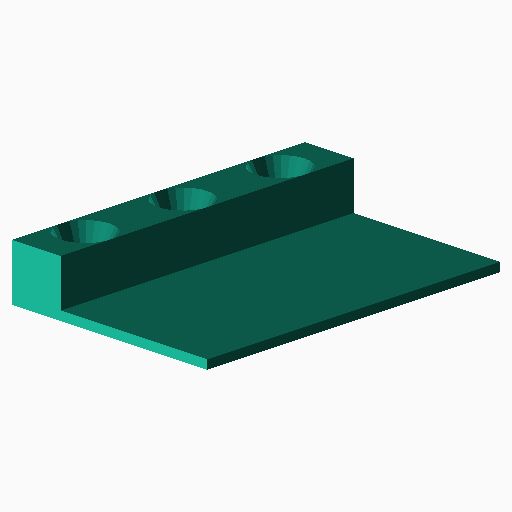
models/printable/foot_mock_toe_spring.png
