chrisspen/saunterbot/models/printable/foot_pivot.png

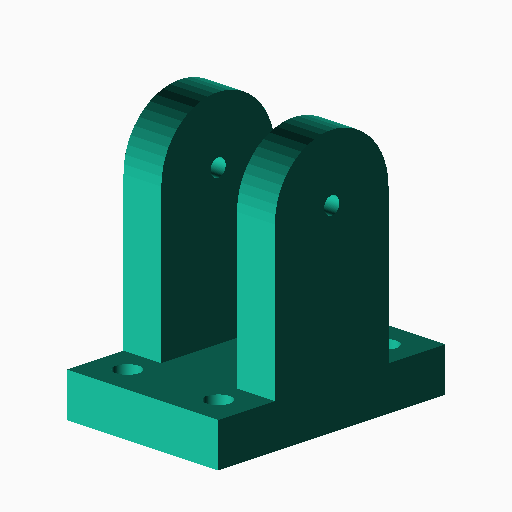
models/printable/foot_pivot.png
