chrisspen/saunterbot/models/printable/leg_hip_axle.png

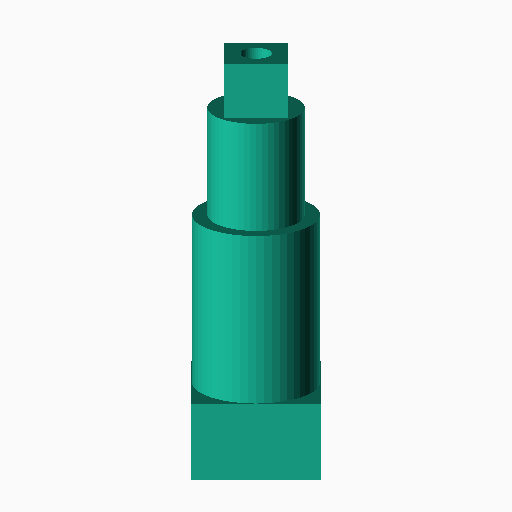
models/printable/leg_hip_axle.png
