chrisspen/saunterbot/models/printable/leg_hip_gear_main.png

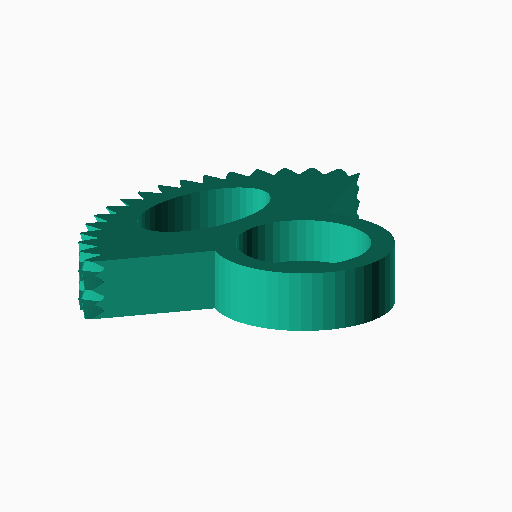
models/printable/leg_hip_gear_main.png
