chrisspen/saunterbot/models/printable/leg_hip_holder.png

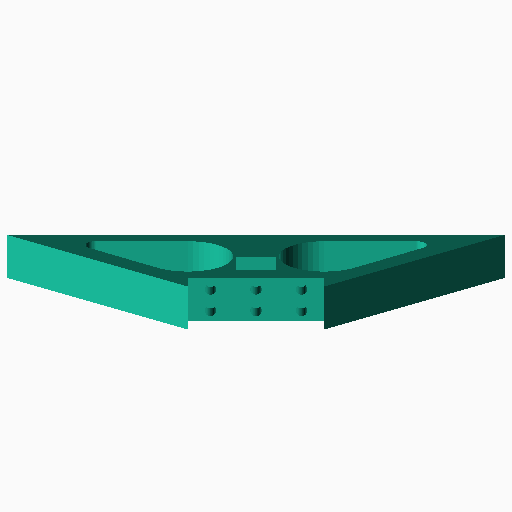
models/printable/leg_hip_holder.png
