chrisspen/saunterbot/models/printable/leg_hip_spacer.png

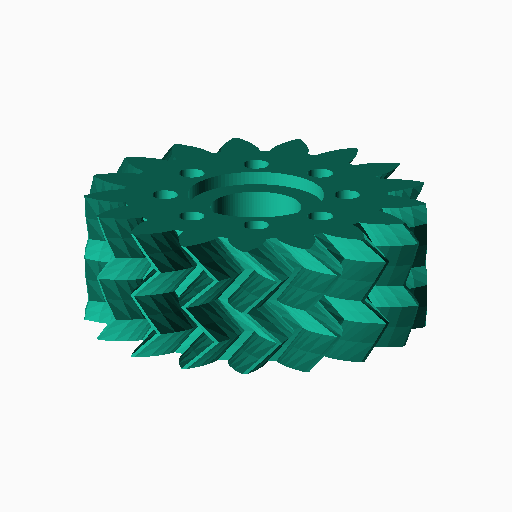
models/printable/leg_hip_spacer.png
