chrisspen/saunterbot/models/printable/leg_hip_tendon_retainer.png

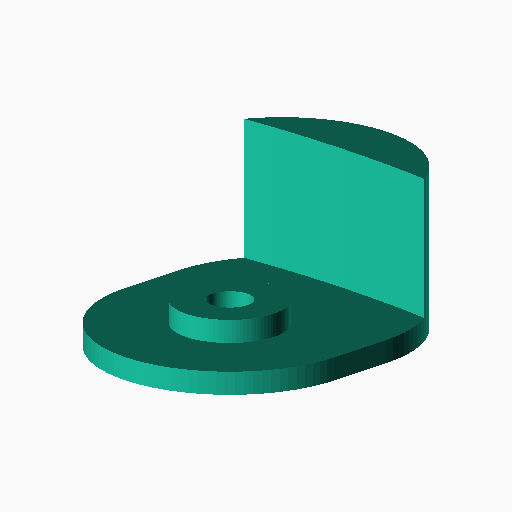
models/printable/leg_hip_tendon_retainer.png
