chrisspen/saunterbot/models/printable/leg_knee_servo_riser.png

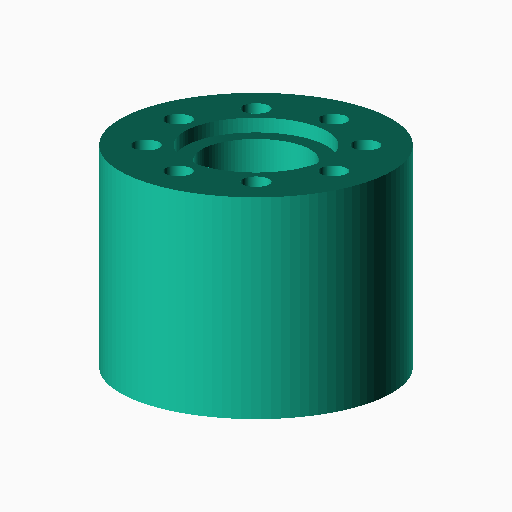
models/printable/leg_knee_servo_riser.png
