chrisspen/saunterbot/models/printable/leg_knee_servo_spindle.png

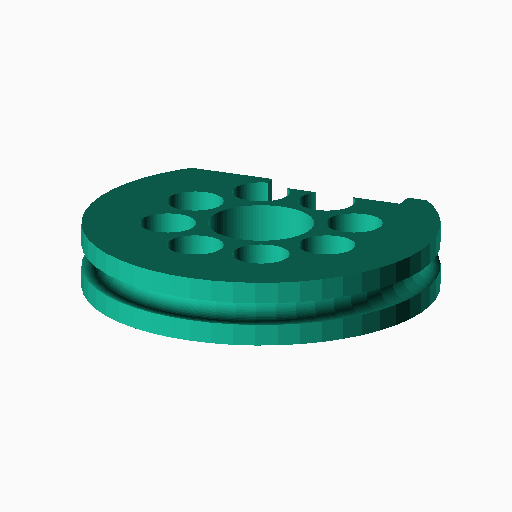
models/printable/leg_knee_servo_spindle.png
