chrisspen/saunterbot/models/printable/leg_knee_tendon_anchor_bottom.png

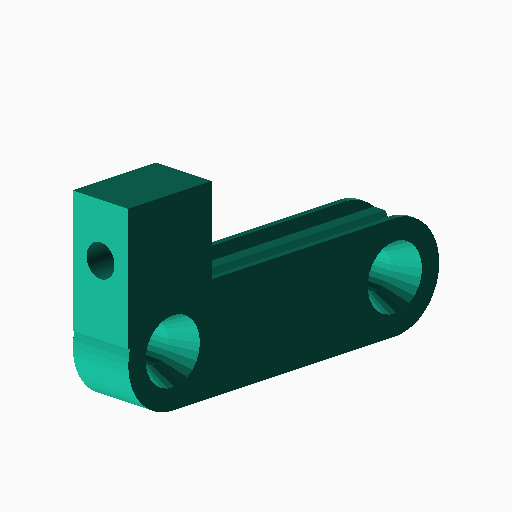
models/printable/leg_knee_tendon_anchor_bottom.png
