chrisspen/saunterbot/models/printable/leg_knee_tendon_anchor_top.png

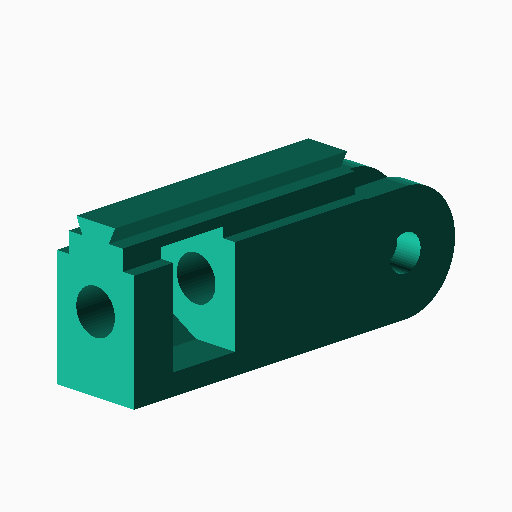
models/printable/leg_knee_tendon_anchor_top.png
