chrisspen/saunterbot/models/printable/leg_spring2.png

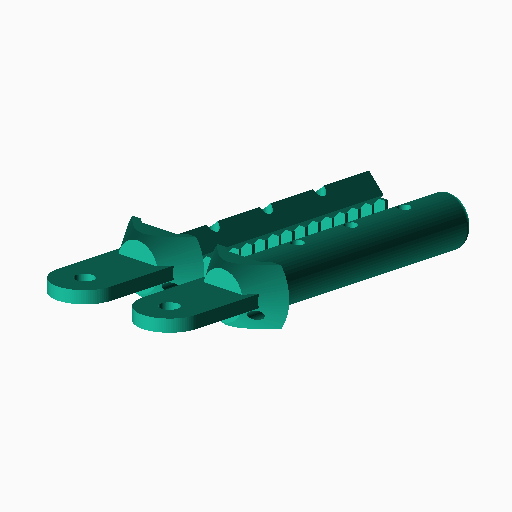
models/printable/leg_spring2.png
