chrisspen/saunterbot/models/printable/leg_spring2_female.png

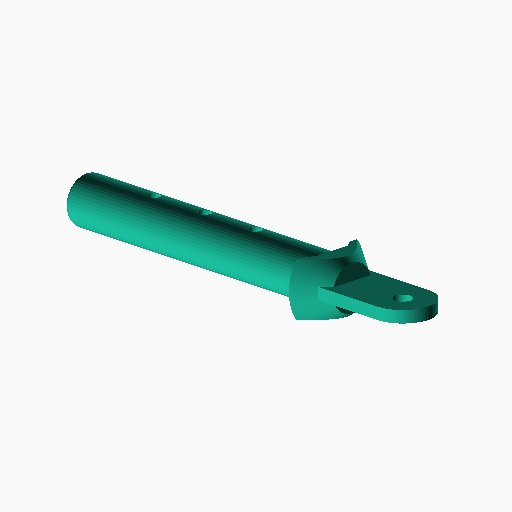
models/printable/leg_spring2_female.png
