chrisspen/saunterbot/models/printable/leg_spring_hinge_extender.png

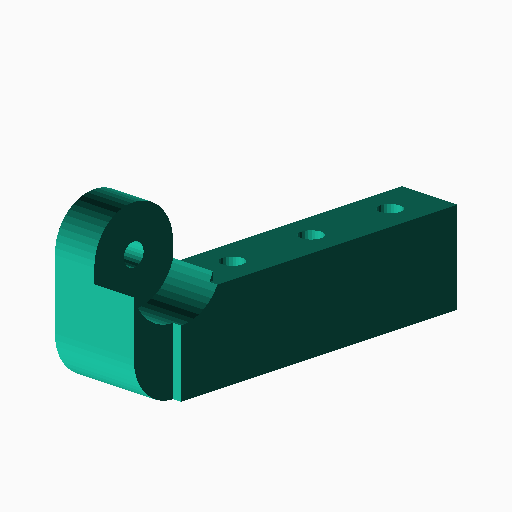
models/printable/leg_spring_hinge_extender.png
