chrisspen/saunterbot/models/printable/leg_spring_hinge_extender_mirrored.png

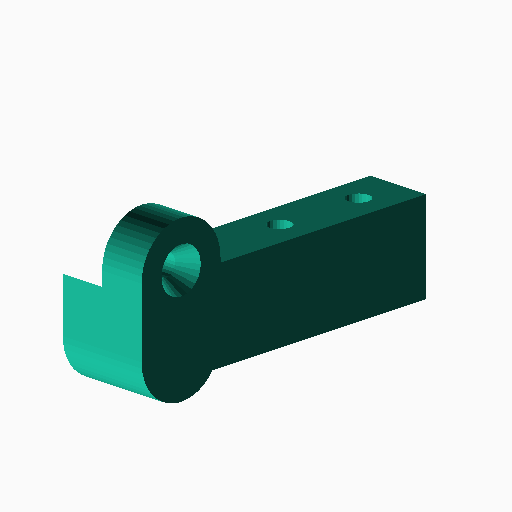
models/printable/leg_spring_hinge_extender_mirrored.png
