chrisspen/saunterbot/models/printable/leg_upper_mirrored.png

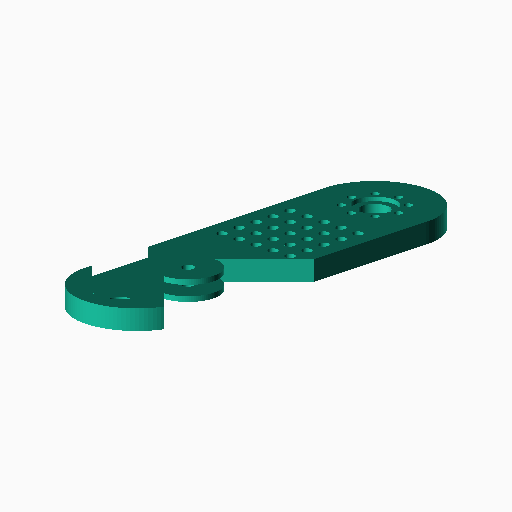
models/printable/leg_upper_mirrored.png
