chrisspen/saunterbot/models/printable/motors_alturn_abrs_5314htg_hv.png

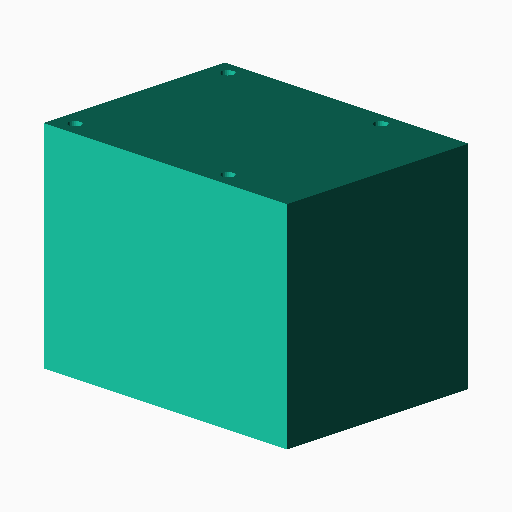
models/printable/motors_alturn_abrs_5314htg_hv.png
