chrisspen/saunterbot/models/printable/pelvis_cross_support.png

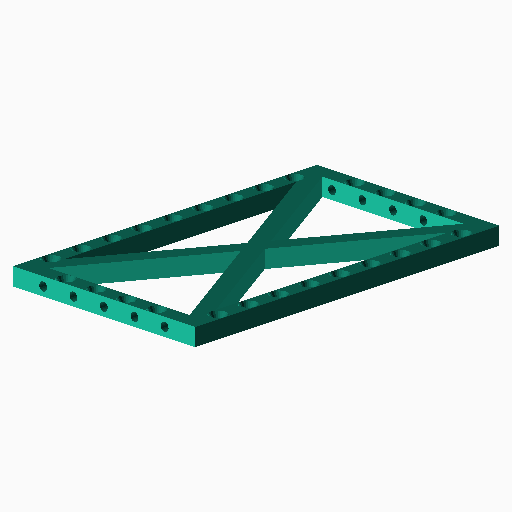
models/printable/pelvis_cross_support.png
