chrisspen/saunterbot/models/printable/pelvis_motor_face.png

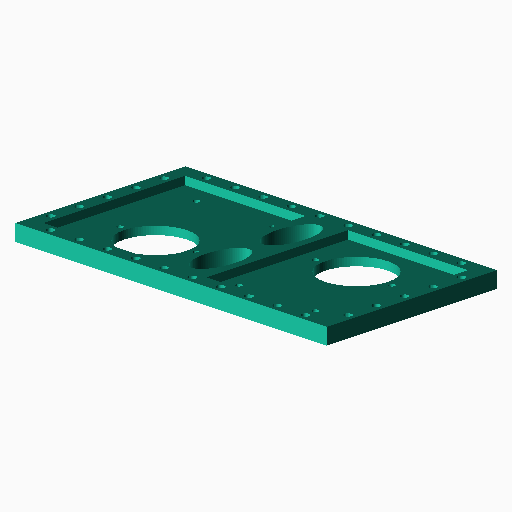
models/printable/pelvis_motor_face.png
