chrisspen/saunterbot/models/printable/pelvis_motor_face_mirrored.png

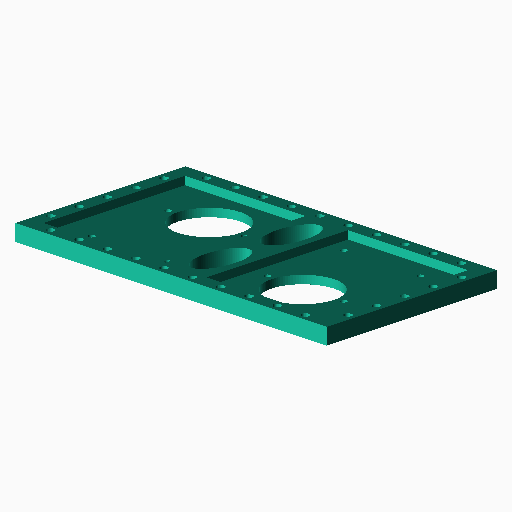
models/printable/pelvis_motor_face_mirrored.png
